0ddjob/Amstrad-CPC/Amstrad_CPC_Keyboard/Connectors/CPC664_Keyboard_Connector.jpeg

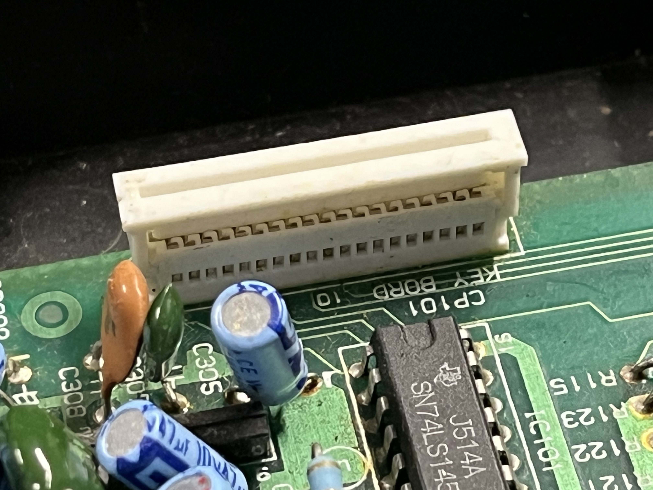
Amstrad_CPC_Keyboard/Connectors/CPC664_Keyboard_Connector.jpeg
