0ddjob/Amstrad-CPC/Amstrad_CPC_Keyboard/Connectors/Later_CPC464_Dual_Keyboard_Connectors.jpeg

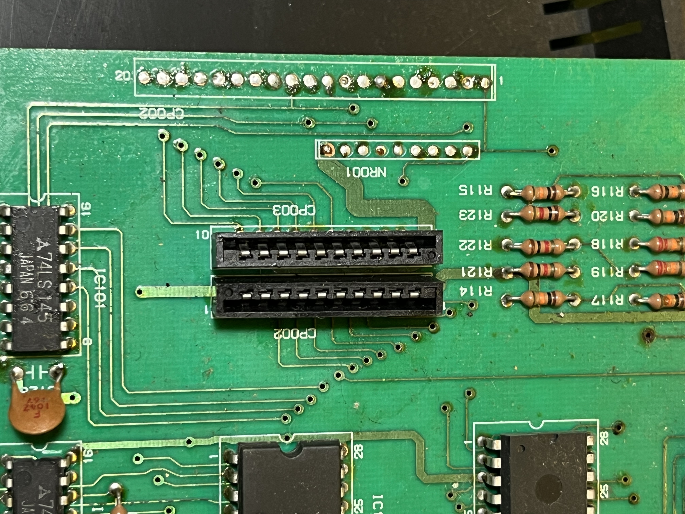
Amstrad_CPC_Keyboard/Connectors/Later_CPC464_Dual_Keyboard_Connectors.jpeg
