0ddjob/Amstrad-CPC/Amstrad_CPC_Keyboard/Connectors/Original_CPC464_20pin_Keyboard_Connector.jpeg

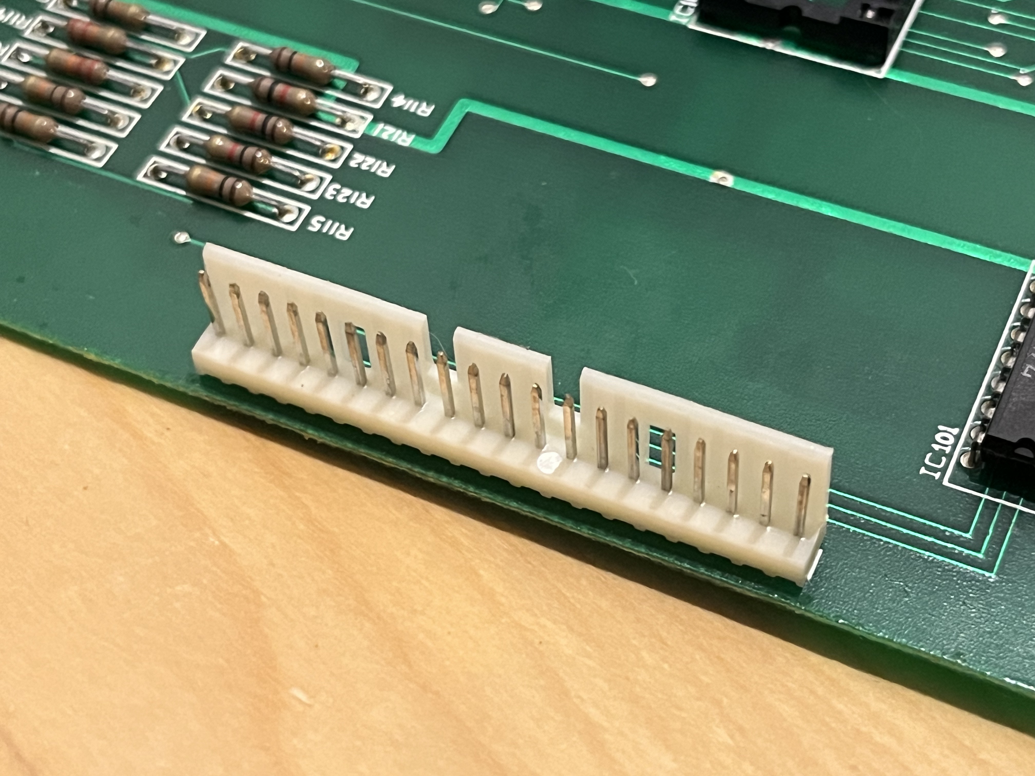
Amstrad_CPC_Keyboard/Connectors/Original_CPC464_20pin_Keyboard_Connector.jpeg
