0ddjob/Amstrad-CPC/Amstrad_CPC_Keyboard/CPC464_CPC664/Keyboard-Layout-Editor/Match_Original_CPC664/amstrad-cpc664_original.jpg

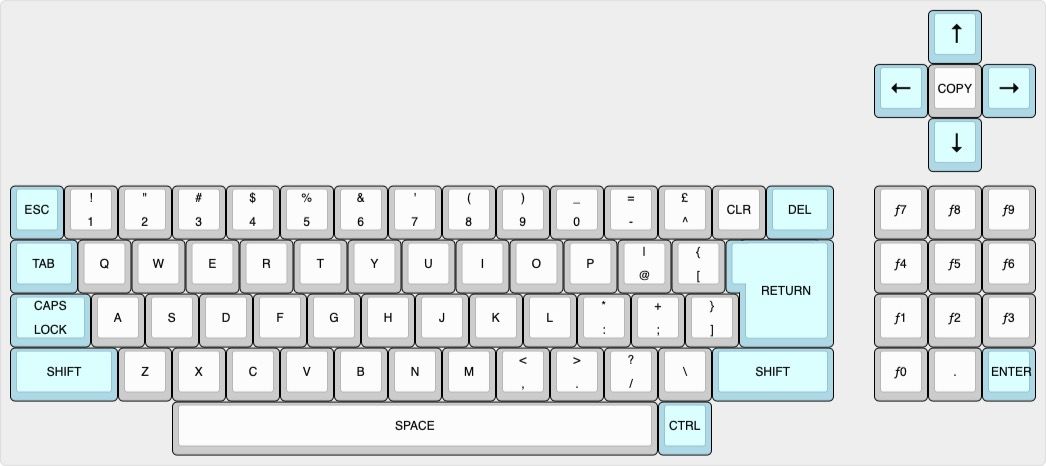
Amstrad_CPC_Keyboard/CPC464_CPC664/Keyboard-Layout-Editor/Match_Original_CPC664/amstrad-cpc664_original.jpg
