0ddjob/Amstrad-CPC/Amstrad_CPC_Keyboard/CPC464_CPC664/Keyboard-Layout-Editor/Modern_Key_Size/amstrad-cpc664_modern.jpg

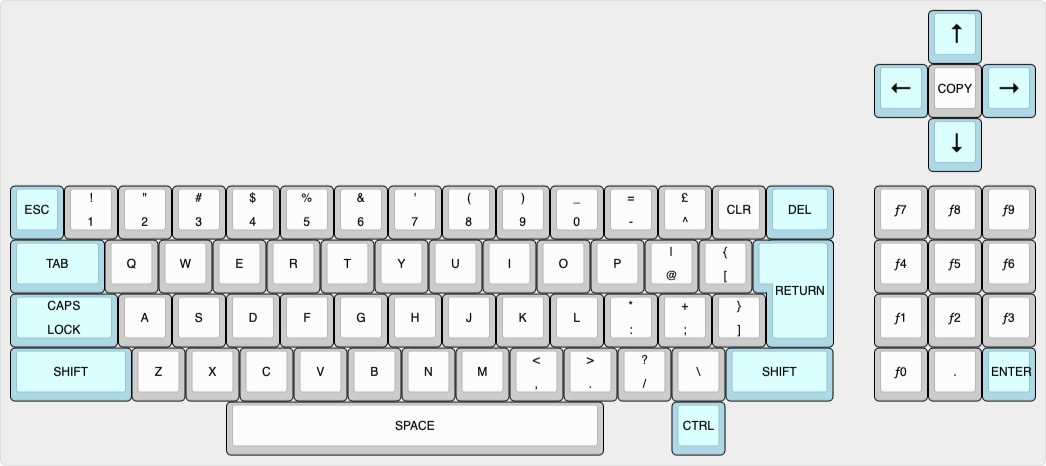
Amstrad_CPC_Keyboard/CPC464_CPC664/Keyboard-Layout-Editor/Modern_Key_Size/amstrad-cpc664_modern.jpg
