0ddjob/Amstrad-CPC/Amstrad_CPC_Keyboard/Datasheets/Amstrad_CPC464_CP002&CP003.jpg

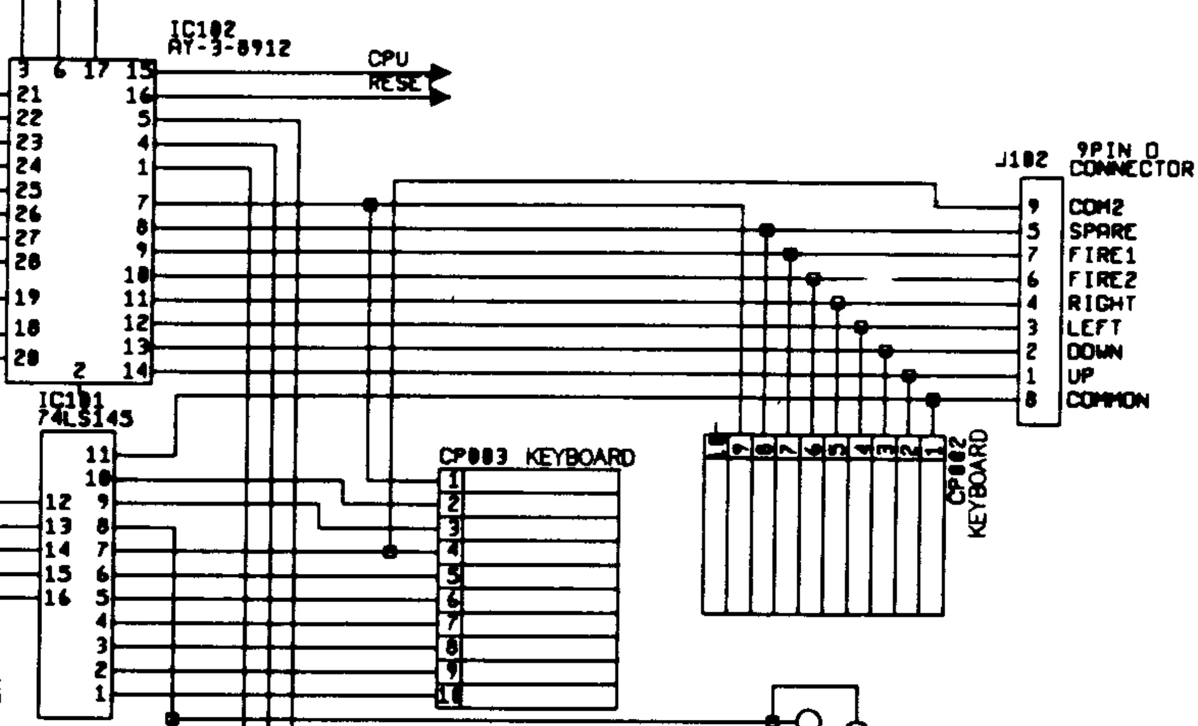
Amstrad_CPC_Keyboard/Datasheets/Amstrad_CPC464_CP002&CP003.jpg
