0ddjob/Amstrad-CPC/Amstrad_CPC_Keyboard/Datasheets/Amstrad_CPC464_MC0044A_Keyboard.jpg

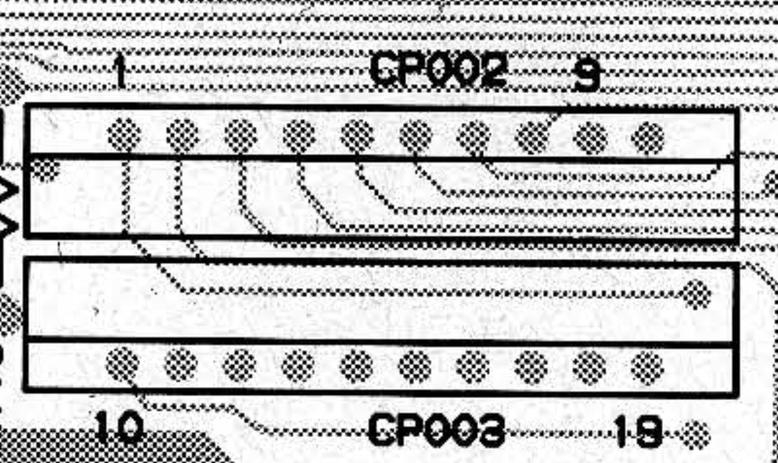
Amstrad_CPC_Keyboard/Datasheets/Amstrad_CPC464_MC0044A_Keyboard.jpg
