0ddjob/Amstrad-CPC/Amstrad_CPC_Keyboard/Schematics/Amstrad_CPC6128_Keyboard_Schematic.png

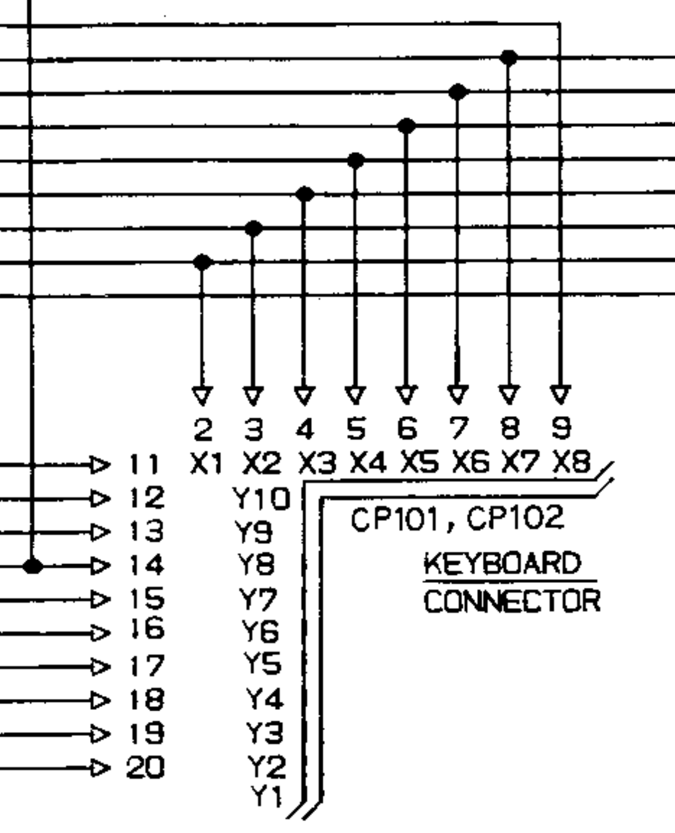
Amstrad_CPC_Keyboard/Schematics/Amstrad_CPC6128_Keyboard_Schematic.png
