0ddjob/Amstrad-CPC/CPC_Plus_Floppy_Adaptor/Amstrad_CPC_Plus_External_drive_connector_pinout.jpg

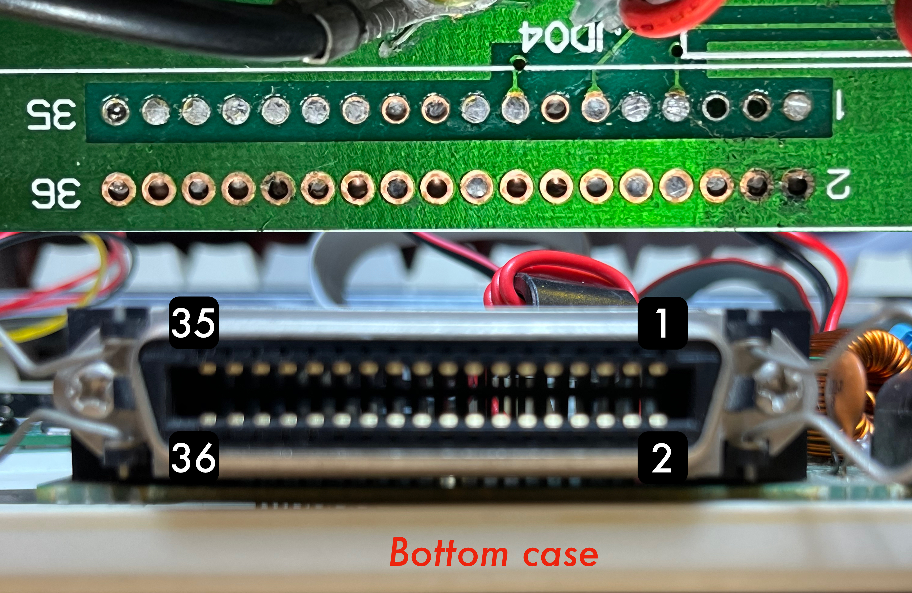
CPC_Plus_Floppy_Adaptor/Amstrad_CPC_Plus_External_drive_connector_pinout.jpg
