0ddjob/Amstrad-CPC/Laserwarp/Sprites/Laserwarp_Sprites.png

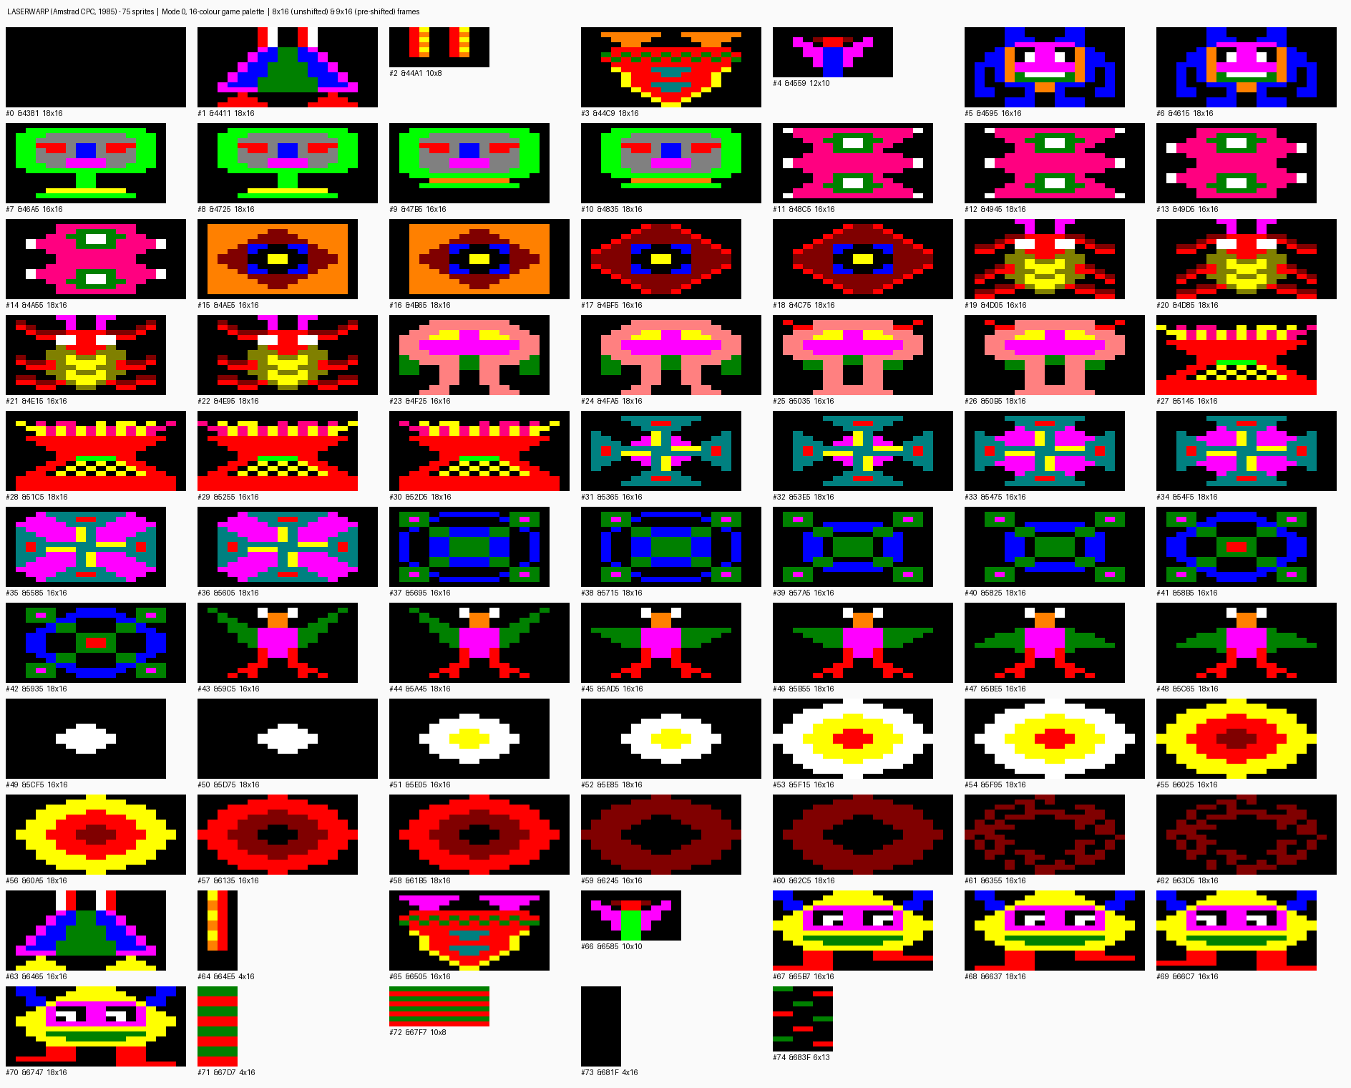
Laserwarp/Sprites/Laserwarp_Sprites.png
