0ddjob/Amstrad-CPC/Laserwarp/Sprites/sprite_01_4411_18x16.png

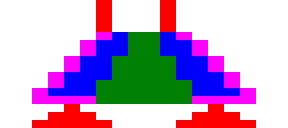
Laserwarp/Sprites/sprite_01_4411_18x16.png
