0ddjob/Amstrad-CPC/Laserwarp/Sprites/sprite_03_44C9_18x16.png

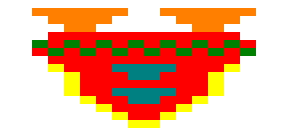
Laserwarp/Sprites/sprite_03_44C9_18x16.png
