0ddjob/Amstrad-CPC/Laserwarp/Sprites/sprite_05_4595_16x16.png

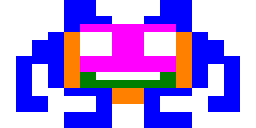
Laserwarp/Sprites/sprite_05_4595_16x16.png
