0ddjob/Amstrad-CPC/Laserwarp/Sprites/sprite_06_4615_18x16.png

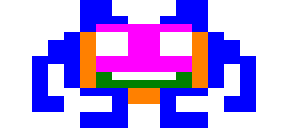
Laserwarp/Sprites/sprite_06_4615_18x16.png
