0ddjob/Amstrad-CPC/Laserwarp/Sprites/sprite_07_46A5_16x16.png

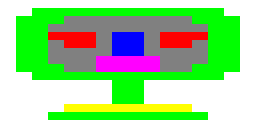
Laserwarp/Sprites/sprite_07_46A5_16x16.png
