0ddjob/Amstrad-CPC/Laserwarp/Sprites/sprite_09_47B5_16x16.png

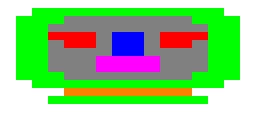
Laserwarp/Sprites/sprite_09_47B5_16x16.png
