0ddjob/Amstrad-CPC/Laserwarp/Sprites/sprite_11_48C5_16x16.png

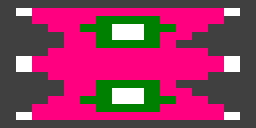
Laserwarp/Sprites/sprite_11_48C5_16x16.png
