0ddjob/Amstrad-CPC/Laserwarp/Sprites/sprite_12_4945_18x16.png

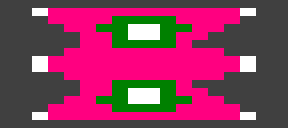
Laserwarp/Sprites/sprite_12_4945_18x16.png
