0ddjob/Amstrad-CPC/Laserwarp/Sprites/sprite_13_49D5_16x16.png

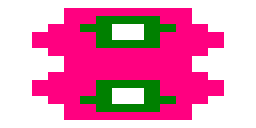
Laserwarp/Sprites/sprite_13_49D5_16x16.png
