0ddjob/Amstrad-CPC/Laserwarp/Sprites/sprite_14_4A55_18x16.png

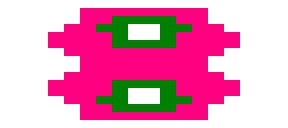
Laserwarp/Sprites/sprite_14_4A55_18x16.png
