0ddjob/Amstrad-CPC/Laserwarp/Sprites/sprite_15_4AE5_16x16.png

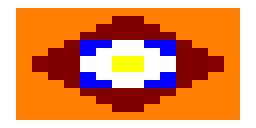
Laserwarp/Sprites/sprite_15_4AE5_16x16.png
