0ddjob/Amstrad-CPC/Laserwarp/Sprites/sprite_17_4BF5_16x16.png

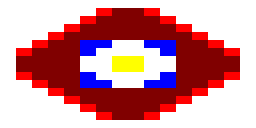
Laserwarp/Sprites/sprite_17_4BF5_16x16.png
