0ddjob/Amstrad-CPC/Laserwarp/Sprites/sprite_18_4C75_18x16.png

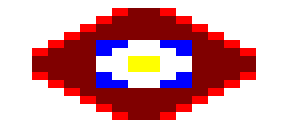
Laserwarp/Sprites/sprite_18_4C75_18x16.png
