0ddjob/Amstrad-CPC/Laserwarp/Sprites/sprite_19_4D05_16x16.png

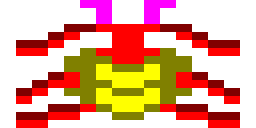
Laserwarp/Sprites/sprite_19_4D05_16x16.png
