0ddjob/Amstrad-CPC/Laserwarp/Sprites/sprite_20_4D85_18x16.png

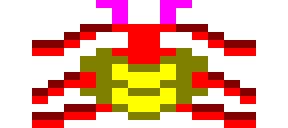
Laserwarp/Sprites/sprite_20_4D85_18x16.png
