0ddjob/Amstrad-CPC/Laserwarp/Sprites/sprite_21_4E15_16x16.png

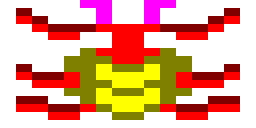
Laserwarp/Sprites/sprite_21_4E15_16x16.png
