0ddjob/Amstrad-CPC/Laserwarp/Sprites/sprite_22_4E95_18x16.png

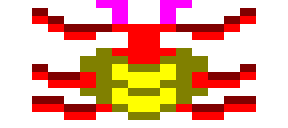
Laserwarp/Sprites/sprite_22_4E95_18x16.png
