0ddjob/Amstrad-CPC/Laserwarp/Sprites/sprite_23_4F25_16x16.png

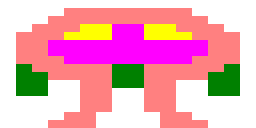
Laserwarp/Sprites/sprite_23_4F25_16x16.png
