0ddjob/Amstrad-CPC/Laserwarp/Sprites/sprite_24_4FA5_18x16.png

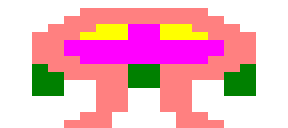
Laserwarp/Sprites/sprite_24_4FA5_18x16.png
