0ddjob/Amstrad-CPC/Laserwarp/Sprites/sprite_25_5035_16x16.png

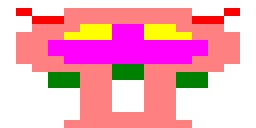
Laserwarp/Sprites/sprite_25_5035_16x16.png
