0ddjob/Amstrad-CPC/Laserwarp/Sprites/sprite_26_50B5_18x16.png

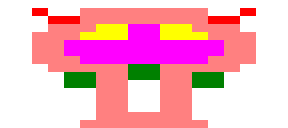
Laserwarp/Sprites/sprite_26_50B5_18x16.png
