0ddjob/Amstrad-CPC/Laserwarp/Sprites/sprite_27_5145_16x16.png

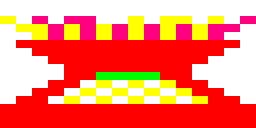
Laserwarp/Sprites/sprite_27_5145_16x16.png
