0ddjob/Amstrad-CPC/Laserwarp/Sprites/sprite_28_51C5_18x16.png

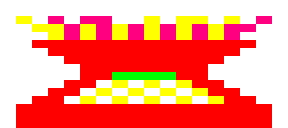
Laserwarp/Sprites/sprite_28_51C5_18x16.png
