0ddjob/Amstrad-CPC/Laserwarp/Sprites/sprite_29_5255_16x16.png

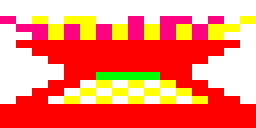
Laserwarp/Sprites/sprite_29_5255_16x16.png
