0ddjob/Amstrad-CPC/Laserwarp/Sprites/sprite_31_5365_16x16.png

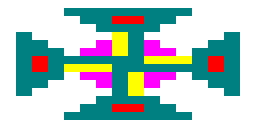
Laserwarp/Sprites/sprite_31_5365_16x16.png
