0ddjob/Amstrad-CPC/Laserwarp/Sprites/sprite_32_53E5_18x16.png

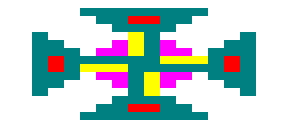
Laserwarp/Sprites/sprite_32_53E5_18x16.png
