0ddjob/Amstrad-CPC/Laserwarp/Sprites/sprite_33_5475_16x16.png

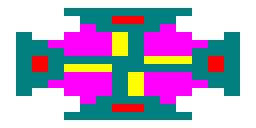
Laserwarp/Sprites/sprite_33_5475_16x16.png
