0ddjob/Amstrad-CPC/Laserwarp/Sprites/sprite_34_54F5_18x16.png

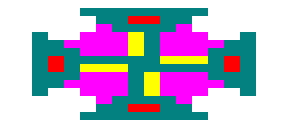
Laserwarp/Sprites/sprite_34_54F5_18x16.png
