0ddjob/Amstrad-CPC/Laserwarp/Sprites/sprite_35_5585_16x16.png

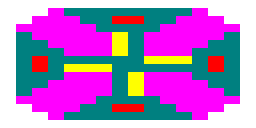
Laserwarp/Sprites/sprite_35_5585_16x16.png
