0ddjob/Amstrad-CPC/Laserwarp/Sprites/sprite_36_5605_18x16.png

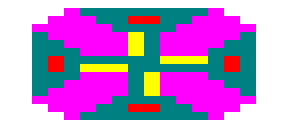
Laserwarp/Sprites/sprite_36_5605_18x16.png
