0ddjob/Amstrad-CPC/Laserwarp/Sprites/sprite_37_5695_16x16.png

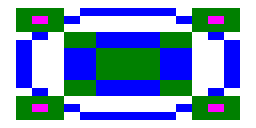
Laserwarp/Sprites/sprite_37_5695_16x16.png
