0ddjob/Amstrad-CPC/Laserwarp/Sprites/sprite_38_5715_18x16.png

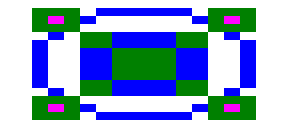
Laserwarp/Sprites/sprite_38_5715_18x16.png
