0ddjob/Amstrad-CPC/Laserwarp/Sprites/sprite_39_57A5_16x16.png

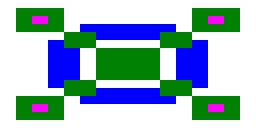
Laserwarp/Sprites/sprite_39_57A5_16x16.png
