0ddjob/Amstrad-CPC/Laserwarp/Sprites/sprite_40_5825_18x16.png

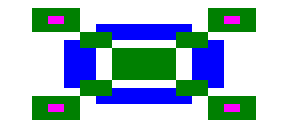
Laserwarp/Sprites/sprite_40_5825_18x16.png
