0ddjob/Amstrad-CPC/Laserwarp/Sprites/sprite_41_58B5_16x16.png

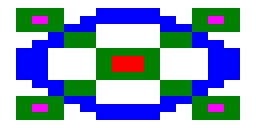
Laserwarp/Sprites/sprite_41_58B5_16x16.png
