0ddjob/Amstrad-CPC/Laserwarp/Sprites/sprite_43_59C5_16x16.png

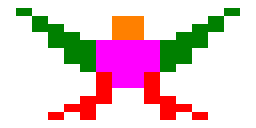
Laserwarp/Sprites/sprite_43_59C5_16x16.png
