0ddjob/Amstrad-CPC/Laserwarp/Sprites/sprite_44_5A45_18x16.png

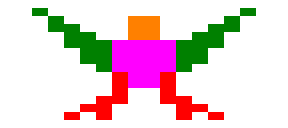
Laserwarp/Sprites/sprite_44_5A45_18x16.png
