0ddjob/Amstrad-CPC/Laserwarp/Sprites/sprite_45_5AD5_16x16.png

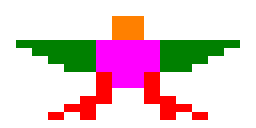
Laserwarp/Sprites/sprite_45_5AD5_16x16.png
