0ddjob/Amstrad-CPC/Laserwarp/Sprites/sprite_47_5BE5_16x16.png

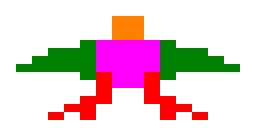
Laserwarp/Sprites/sprite_47_5BE5_16x16.png
