0ddjob/Amstrad-CPC/Laserwarp/Sprites/sprite_48_5C65_18x16.png

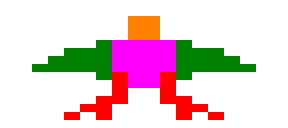
Laserwarp/Sprites/sprite_48_5C65_18x16.png
