0ddjob/Amstrad-CPC/Laserwarp/Sprites/sprite_49_5CF5_16x16.png

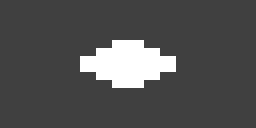
Laserwarp/Sprites/sprite_49_5CF5_16x16.png
