0ddjob/Amstrad-CPC/Laserwarp/Sprites/sprite_50_5D75_18x16.png

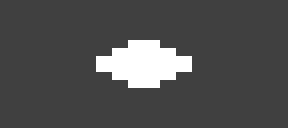
Laserwarp/Sprites/sprite_50_5D75_18x16.png
