0ddjob/Amstrad-CPC/Laserwarp/Sprites/sprite_51_5E05_16x16.png

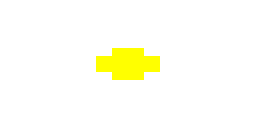
Laserwarp/Sprites/sprite_51_5E05_16x16.png
