0ddjob/Amstrad-CPC/Laserwarp/Sprites/sprite_53_5F15_16x16.png

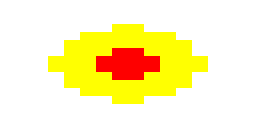
Laserwarp/Sprites/sprite_53_5F15_16x16.png
