0ddjob/Amstrad-CPC/Laserwarp/Sprites/sprite_54_5F95_18x16.png

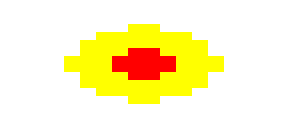
Laserwarp/Sprites/sprite_54_5F95_18x16.png
