0ddjob/Amstrad-CPC/Laserwarp/Sprites/sprite_55_6025_16x16.png

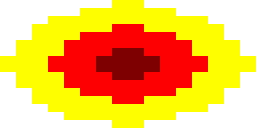
Laserwarp/Sprites/sprite_55_6025_16x16.png
