0ddjob/Amstrad-CPC/Laserwarp/Sprites/sprite_56_60A5_18x16.png

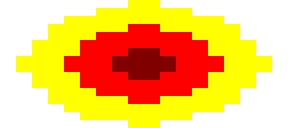
Laserwarp/Sprites/sprite_56_60A5_18x16.png
