0ddjob/Amstrad-CPC/Laserwarp/Sprites/sprite_57_6135_16x16.png

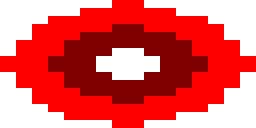
Laserwarp/Sprites/sprite_57_6135_16x16.png
