0ddjob/Amstrad-CPC/Laserwarp/Sprites/sprite_58_61B5_18x16.png

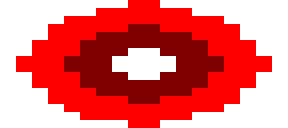
Laserwarp/Sprites/sprite_58_61B5_18x16.png
