0ddjob/Amstrad-CPC/Laserwarp/Sprites/sprite_59_6245_16x16.png

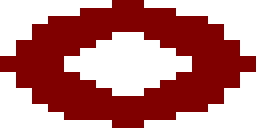
Laserwarp/Sprites/sprite_59_6245_16x16.png
