0ddjob/Amstrad-CPC/Laserwarp/Sprites/sprite_61_6355_16x16.png

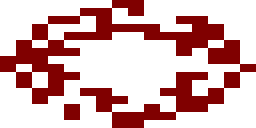
Laserwarp/Sprites/sprite_61_6355_16x16.png
