0ddjob/Amstrad-CPC/Laserwarp/Sprites/sprite_62_63D5_18x16.png

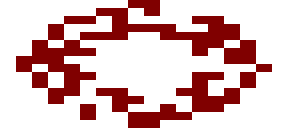
Laserwarp/Sprites/sprite_62_63D5_18x16.png
