0ddjob/Amstrad-CPC/Laserwarp/Sprites/sprite_63_6465_16x16.png

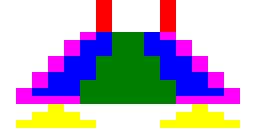
Laserwarp/Sprites/sprite_63_6465_16x16.png
