0ddjob/Amstrad-CPC/Laserwarp/Sprites/sprite_70_6747_18x16.png

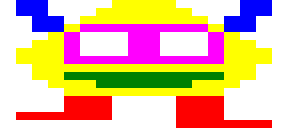
Laserwarp/Sprites/sprite_70_6747_18x16.png
