0ddjob/Amstrad-CPC/VGA4CPC_Brett/Comparator_Board/Comparator_Board_3D.png

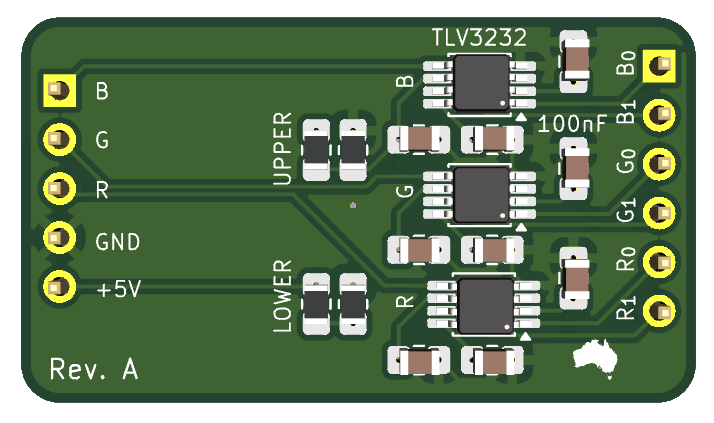
VGA4CPC_Brett/Comparator_Board/Comparator_Board_3D.png
