0ddjob/Amstrad-CPC/Amstrad_CPC_Keyboard/Amstrad_CPC_Tactile-6mm_Troubleshooting_Keyboard.png

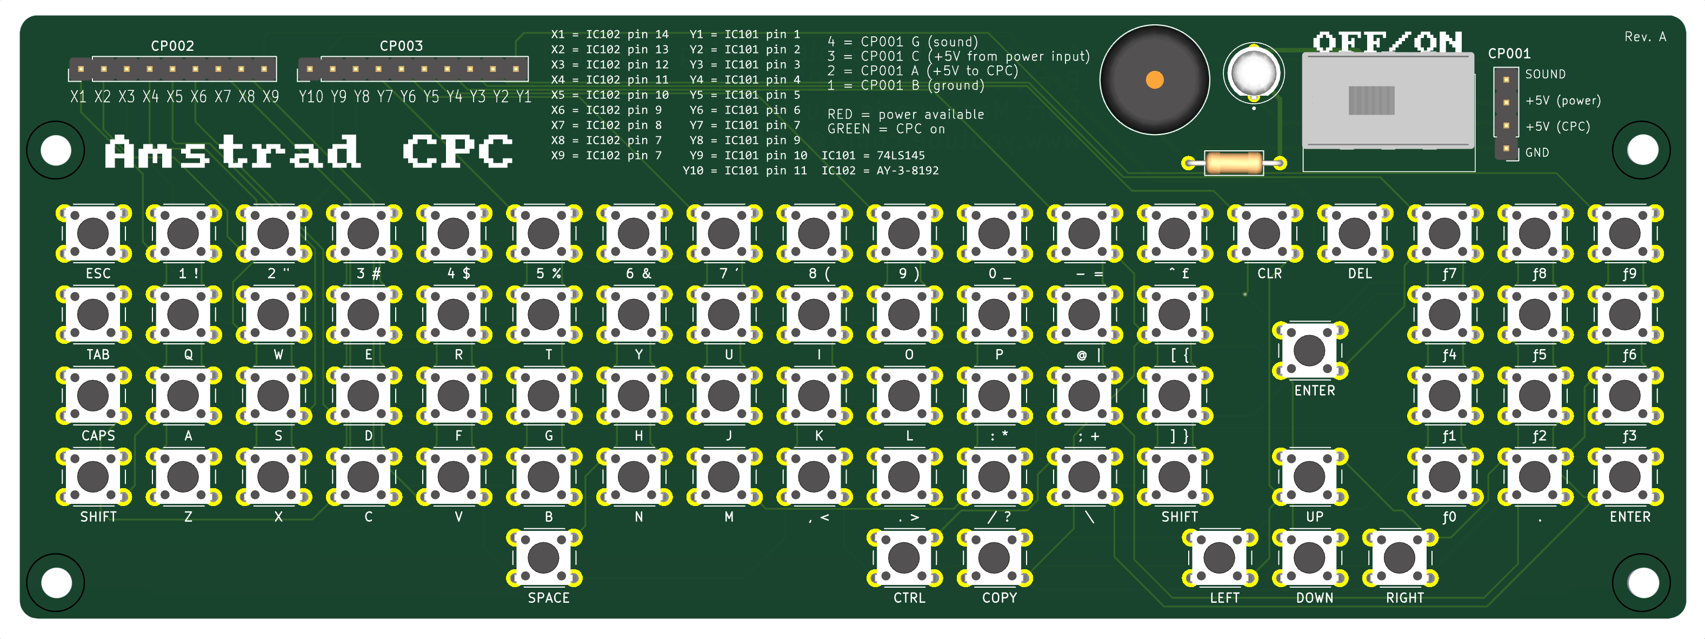
Amstrad_CPC_Keyboard/Amstrad_CPC_Tactile-6mm_Troubleshooting_Keyboard.png
