0ddjob/Amstrad-CPC/Amstrad_CPC_Keyboard/Amstrad_CPC_Tactile-12mm_Troubleshooting_Keyboard_Built.png

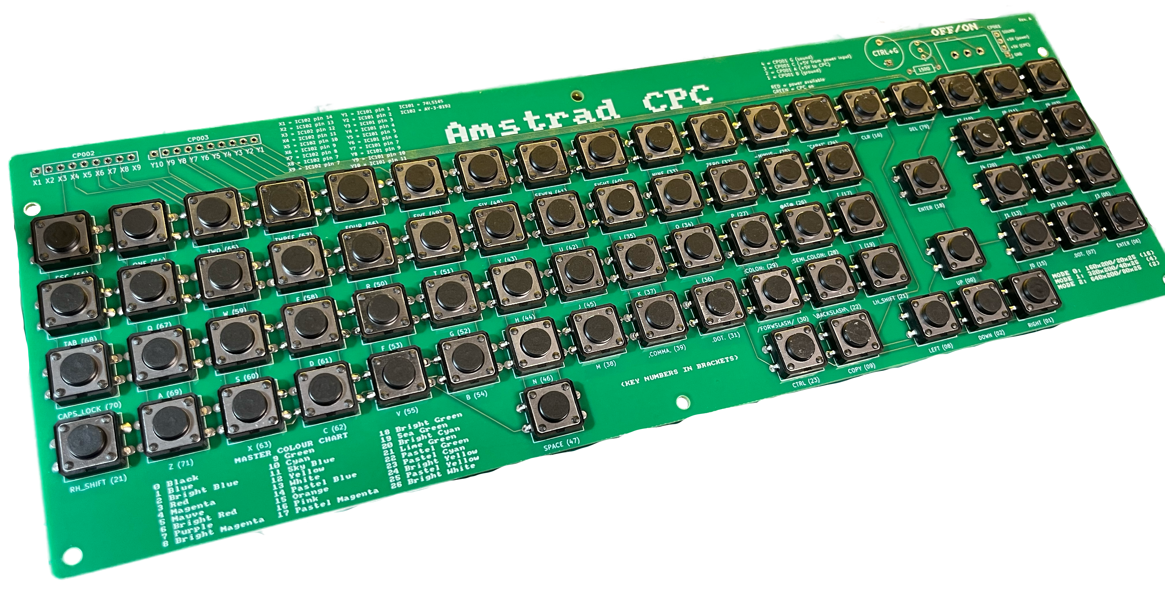
Amstrad_CPC_Keyboard/Amstrad_CPC_Tactile-12mm_Troubleshooting_Keyboard_Built.png
