0ddjob/Amstrad-CPC/Amstrad_CPC_Keyboard/Amstrad_CPC_Tactile_Troubleshooting_Keyboard.png

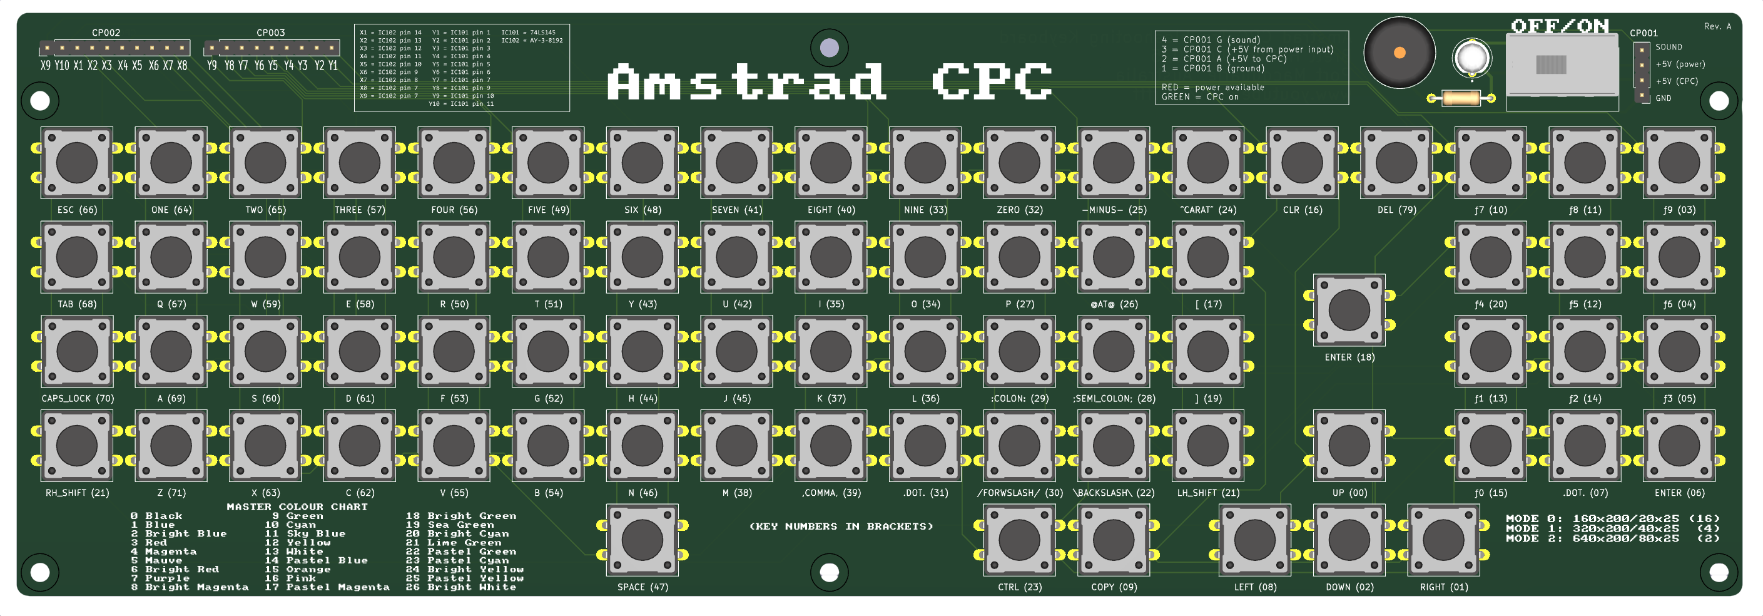
Amstrad_CPC_Keyboard/Amstrad_CPC_Tactile_Troubleshooting_Keyboard.png
