0ddjob/Amstrad-CPC/VGA4CPC_Brett/RevD/VGA4CPC_Brett_RevD_Schematic.pdf

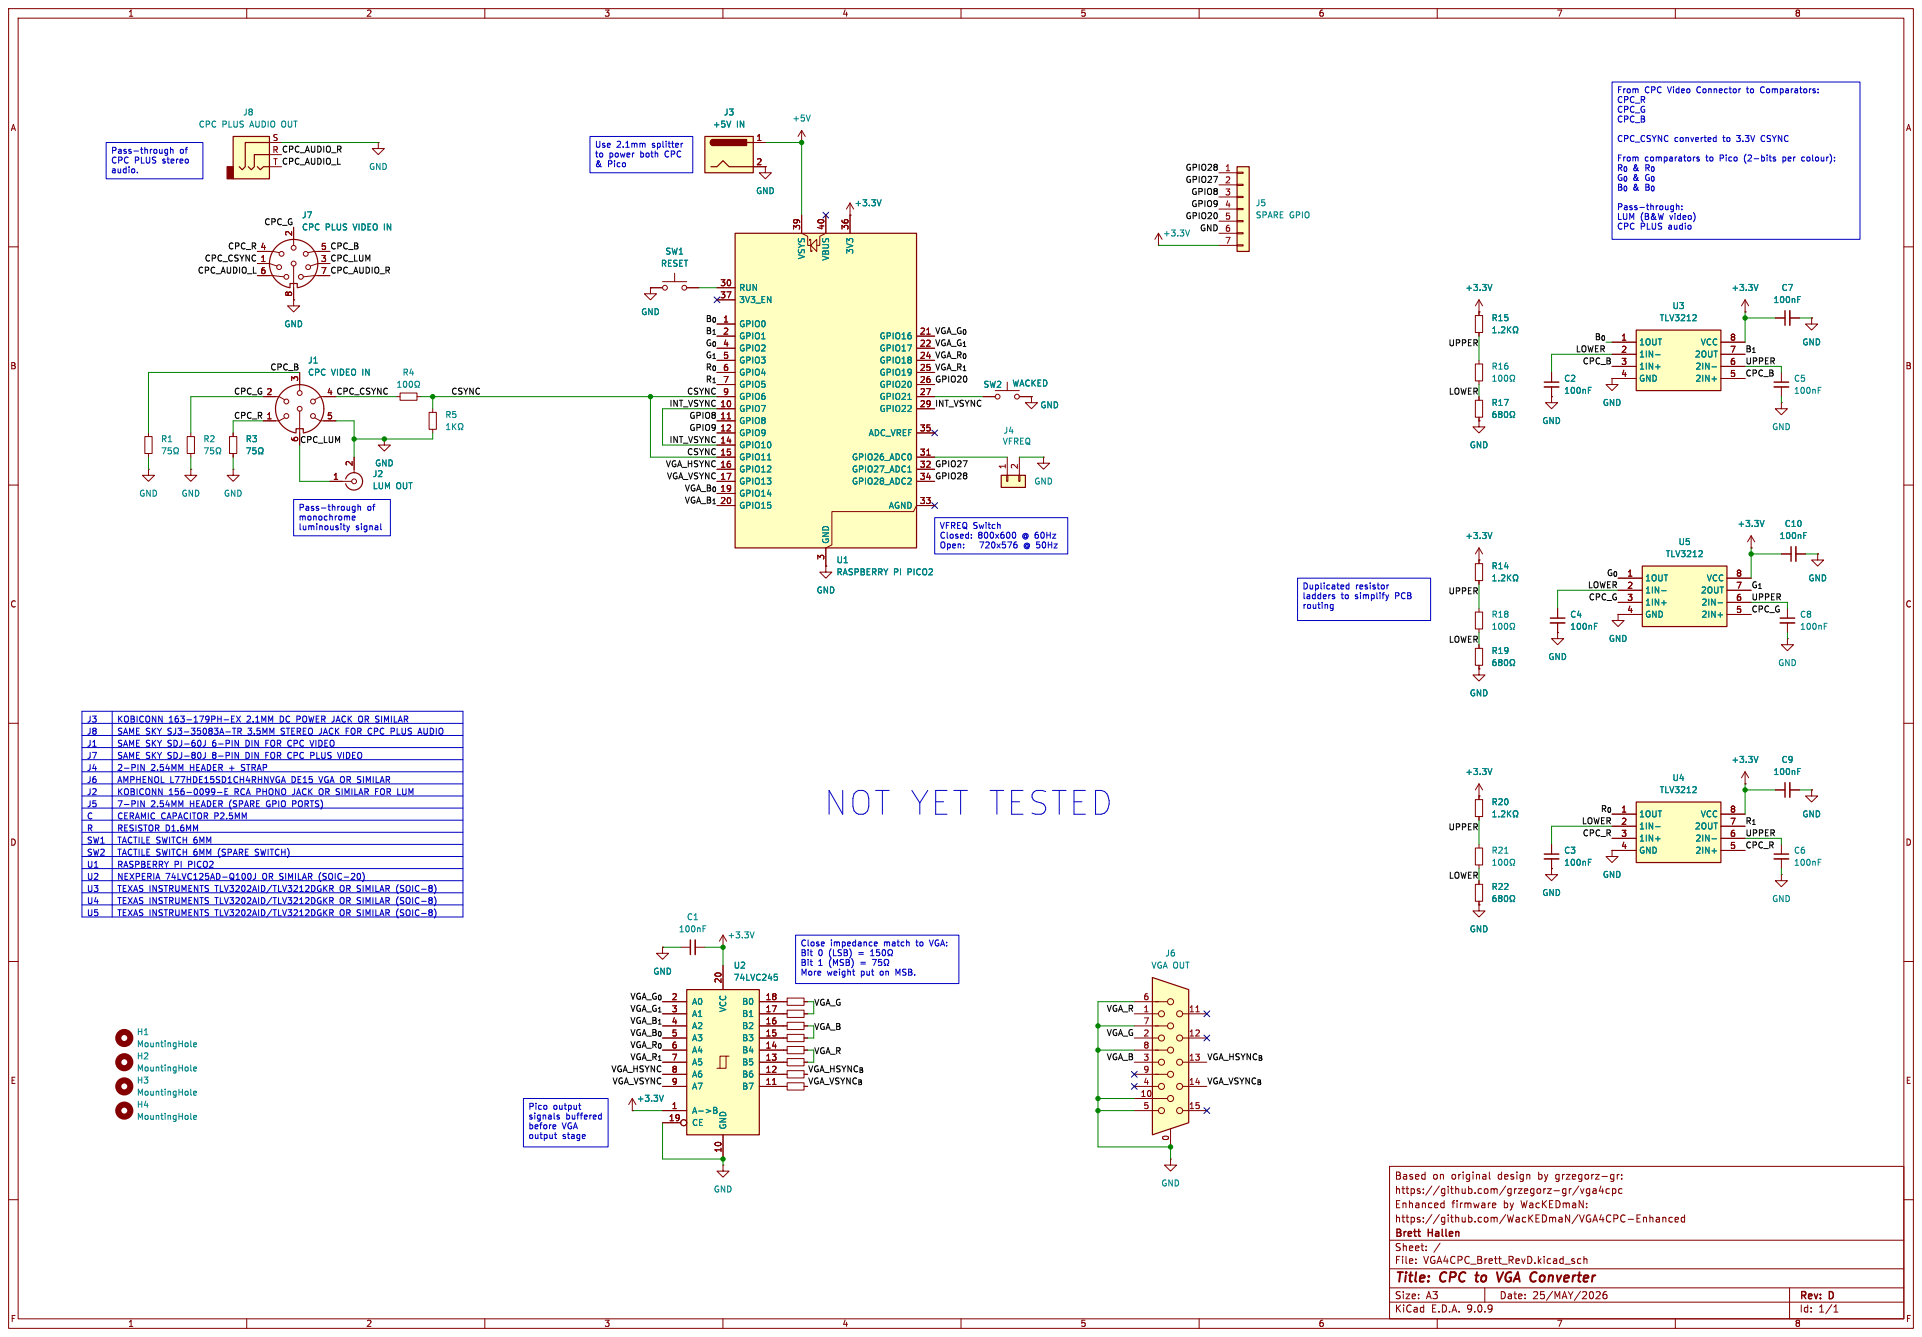
[picture p103: page 1]

to power both CPC

Pass-through: LUM (B&W video) CPC PLUS audio NOT YET TESTED

routing Pico output signals buffered

Bit 1 (MSB) = þÿ75© More weight put on MSB.
