0ddjob/Amstrad-CPC/Amstrad_CPC_Keyboard/CPC6128/Tactile_12mm/Amstrad_Tactile-12mm_Keyboard.kicad_pcb

## KiCad design Amstrad_CPC_Keyboard/CPC6128/Tactile_12mm/Amstrad_Tactile-12mm_Keyboard.kicad_pcb (2025-08-01)

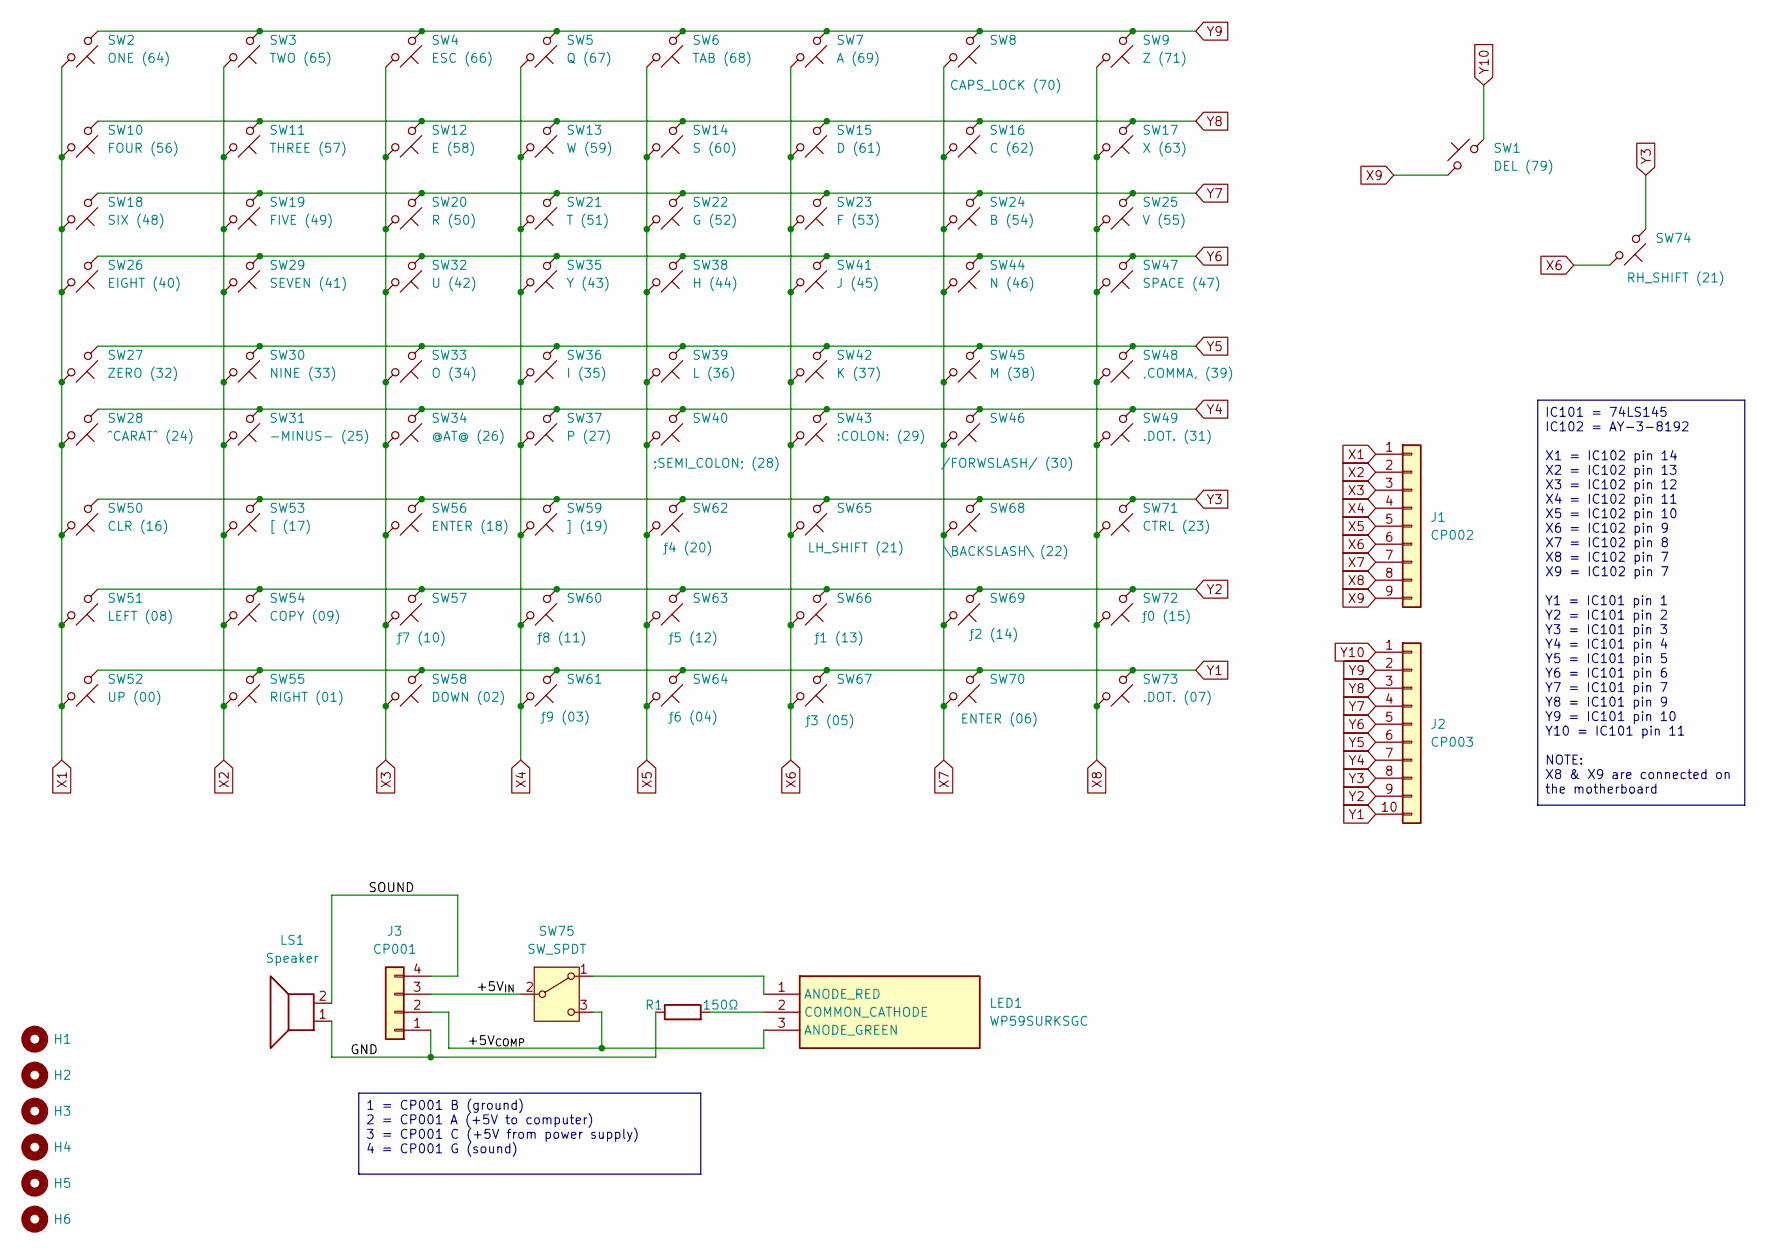
[picture p120: schematic Amstrad_Tactile-12mm_Keyboard.kicad_sch, Amstrad CPC Troubleshooting Keyboard (Tactile)]

Parts:
H1, H2, H3, H4, H5, H6: MountingHole; MountingHole_3.2mm_M3
J1: CP002; PinHeader_1x09_P2.54mm_Vertical
J2: CP003; PinHeader_1x10_P2.54mm_Vertical
J3: CP001; PinHeader_1x04_P2.54mm_Vertical
LED1: WP59SURKSGC; WP59EGC; Mouser Part Number 604-WP59SURKSGC
LS1: Speaker; Buzzer_12x9.5RM7.6
R1: 150Ω; R_Axial_DIN0207_L6.3mm_D2.5mm_P10.16mm_Horizontal
SW1: DEL (79); SW_PUSH-12mm
SW2: ONE (64); SW_PUSH-12mm
SW3: TWO (65); SW_PUSH-12mm
SW4: ESC (66); SW_PUSH-12mm
SW5: Q (67); SW_PUSH-12mm
SW6: TAB (68); SW_PUSH-12mm
SW7: A (69); SW_PUSH-12mm
SW8: CAPS_LOCK (70); SW_PUSH-12mm
SW9: Z (71); SW_PUSH-12mm
SW10: FOUR (56); SW_PUSH-12mm
SW11: THREE (57); SW_PUSH-12mm
SW12: E (58); SW_PUSH-12mm
SW13: W (59); SW_PUSH-12mm
SW14: S (60); SW_PUSH-12mm
SW15: D (61); SW_PUSH-12mm
SW16: C (62); SW_PUSH-12mm
SW17: X (63); SW_PUSH-12mm
SW18: SIX (48); SW_PUSH-12mm
SW19: FIVE (49); SW_PUSH-12mm
SW20: R (50); SW_PUSH-12mm
SW21: T (51); SW_PUSH-12mm
SW22: G (52); SW_PUSH-12mm
SW23: F (53); SW_PUSH-12mm
SW24: B (54); SW_PUSH-12mm
SW25: V (55); SW_PUSH-12mm
SW26: EIGHT (40); SW_PUSH-12mm
SW27: ZERO (32); SW_PUSH-12mm
SW28: ^CARAT^ (24); SW_PUSH-12mm
SW29: SEVEN (41); SW_PUSH-12mm
SW30: NINE (33); SW_PUSH-12mm
SW31: -MINUS- (25); SW_PUSH-12mm
SW32: U (42); SW_PUSH-12mm
SW33: O (34); SW_PUSH-12mm
SW34: @AT@ (26); SW_PUSH-12mm
SW35: Y (43); SW_PUSH-12mm
SW36: I (35); SW_PUSH-12mm
SW37: P (27); SW_PUSH-12mm
SW38: H (44); SW_PUSH-12mm
SW39: L (36); SW_PUSH-12mm
SW40: ;SEMI_COLON; (28); SW_PUSH-12mm
SW41: J (45); SW_PUSH-12mm
SW42: K (37); SW_PUSH-12mm
SW43: :COLON: (29); SW_PUSH-12mm
SW44: N (46); SW_PUSH-12mm
SW45: M (38); SW_PUSH-12mm
SW46: /FORWSLASH/ (30); SW_PUSH-12mm
SW47: SPACE (47); SW_PUSH-12mm
SW48: ,COMMA, (39); SW_PUSH-12mm
SW49: .DOT. (31); SW_PUSH-12mm
SW50: CLR (16); SW_PUSH-12mm
SW51: LEFT (08); SW_PUSH-12mm
SW52: UP (00); SW_PUSH-12mm
SW53: [ (17); SW_PUSH-12mm
SW54: COPY (09); SW_PUSH-12mm
SW55: RIGHT (01); SW_PUSH-12mm
SW56: ENTER (18); SW_PUSH-12mm
SW57: ƒ7 (10); SW_PUSH-12mm
SW58: DOWN (02); SW_PUSH-12mm
SW59: ] (19); SW_PUSH-12mm
SW60: ƒ8 (11); SW_PUSH-12mm
SW61: ƒ9 (03); SW_PUSH-12mm
SW62: ƒ4 (20); SW_PUSH-12mm
SW63: ƒ5 (12); SW_PUSH-12mm
SW64: ƒ6 (04); SW_PUSH-12mm
SW65: LH_SHIFT (21); SW_PUSH-12mm
SW66: ƒ1 (13); SW_PUSH-12mm
SW67: ƒ3 (05); SW_PUSH-12mm
SW68: \BACKSLASH\ (22); SW_PUSH-12mm
SW69: ƒ2 (14); SW_PUSH-12mm
SW70: ENTER (06); SW_PUSH-12mm
SW71: CTRL (23); SW_PUSH-12mm
SW72: ƒ0 (15); SW_PUSH-12mm
SW73: .DOT. (07); SW_PUSH-12mm
SW74: RH_SHIFT (21); SW_PUSH-12mm
SW75: SW_SPDT; L102011MS02Q

Connections:
/+5V_{COMP}: J3.2, LED1.3 (ANODE_GREEN), SW75.3 (C)
/+5V_{IN}: J3.3, SW75.2 (B)
/GND: J3.1, LS1.1, R1.1
/SOUND: J3.4, LS1.2
unnamed: LED1.1 (ANODE_RED), SW75.1 (A)
unnamed: LED1.2 (COMMON_CATHODE), R1.2
X1: J1.1, SW2.2, SW10.2, SW18.2, SW26.2, SW27.2, SW28.2, SW50.2, SW51.2, SW52.2
X2: J1.2, SW3.2, SW11.2, SW19.2, SW29.2, SW30.2, SW31.2, SW53.2, SW54.2, SW55.2
X3: J1.3, SW4.2, SW12.2, SW20.2, SW32.2, SW33.2, SW34.2, SW56.2, SW57.2, SW58.2
X4: J1.4, SW5.2, SW13.2, SW21.2, SW35.2, SW36.2, SW37.2, SW59.2, SW60.2, SW61.2
X5: J1.5, SW6.2, SW14.2, SW22.2, SW38.2, SW39.2, SW40.2, SW62.2, SW63.2, SW64.2
X6: J1.6, SW7.2, SW15.2, SW23.2, SW41.2, SW42.2, SW43.2, SW65.2, SW66.2, SW67.2, SW74.2
X7: J1.7, SW8.2, SW16.2, SW24.2, SW44.2, SW45.2, SW46.2, SW68.2, SW69.2, SW70.2
X8: J1.8, SW9.2, SW17.2, SW25.2, SW47.2, SW48.2, SW49.2, SW71.2, SW72.2, SW73.2
X9: J1.9, SW1.1
Y1: J2.10, SW52.1, SW55.1, SW58.1, SW61.1, SW64.1, SW67.1, SW70.1, SW73.1
Y2: J2.9, SW51.1, SW54.1, SW57.1, SW60.1, SW63.1, SW66.1, SW69.1, SW72.1
Y3: J2.8, SW50.1, SW53.1, SW56.1, SW59.1, SW62.1, SW65.1, SW68.1, SW71.1, SW74.1
Y4: J2.7, SW28.1, SW31.1, SW34.1, SW37.1, SW40.1, SW43.1, SW46.1, SW49.1
Y5: J2.6, SW27.1, SW30.1, SW33.1, SW36.1, SW39.1, SW42.1, SW45.1, SW48.1
Y6: J2.5, SW26.1, SW29.1, SW32.1, SW35.1, SW38.1, SW41.1, SW44.1, SW47.1
Y7: J2.4, SW18.1, SW19.1, SW20.1, SW21.1, SW22.1, SW23.1, SW24.1, SW25.1
Y8: J2.3, SW10.1, SW11.1, SW12.1, SW13.1, SW14.1, SW15.1, SW16.1, SW17.1
Y9: J2.2, SW2.1, SW3.1, SW4.1, SW5.1, SW6.1, SW7.1, SW8.1, SW9.1
Y10: J2.1, SW1.2

Notes on the sheet:
1 = CP001 B (ground) 2 = CP001 A (+5V to computer) 3 = CP001 C (+5V from power supply) 4 = CP001 G (sound)
IC101 = 74LS145 IC102 = AY-3-8192 X1 = IC102 pin 14 X2 = IC102 pin 13 X3 = IC102 pin 12 X4 = IC102 pin 11 X5 = IC102 pin 10 X6 = IC102 pin 9 X7 = IC102 pin 8 X8 = IC102 pin 7 X9 = IC102 pin 7 Y1 = IC101 pin 1 Y2 = IC101 pin 2 Y3 = IC101 pin 3 Y4 = IC101 pin 4 Y5 = IC101 pin 5 Y6 = IC101 pin 6 Y7 = 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

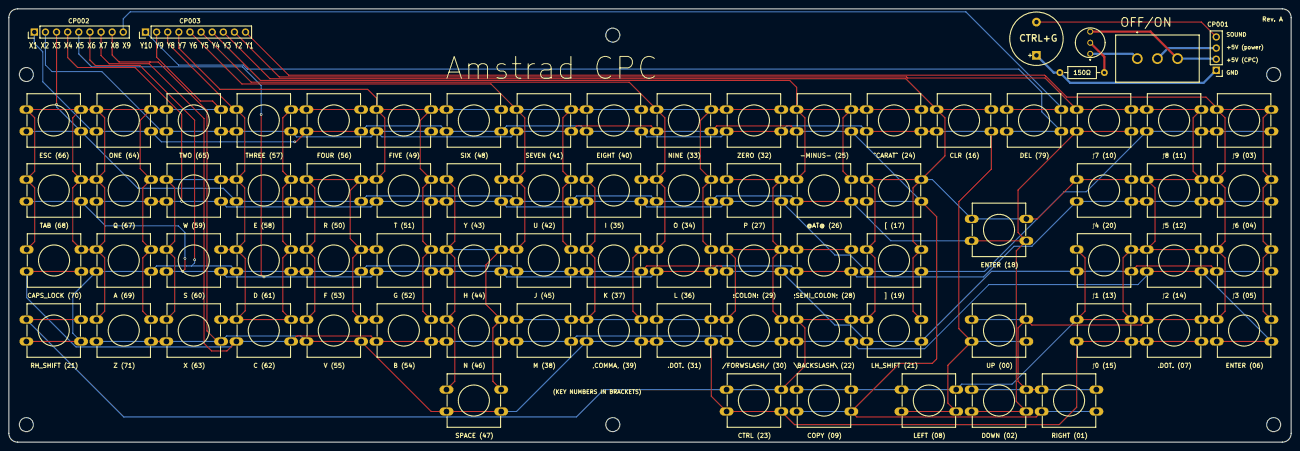
[picture p121: board Amstrad_Tactile-12mm_Keyboard.kicad_pcb from above]

Board: 2 copper layers, 293.0 x 99.0 mm, 87 parts (0 on the bottom side), 25 nets.
