0ddjob/Amstrad-CPC/CPC_PICOROM_PLUS/Hardware/Kicad/CPC_PICOROM_PLUS.kicad_pcb

## KiCad design CPC_PICOROM_PLUS/Hardware/Kicad/CPC_PICOROM_PLUS.kicad_pcb (2025-07-30)

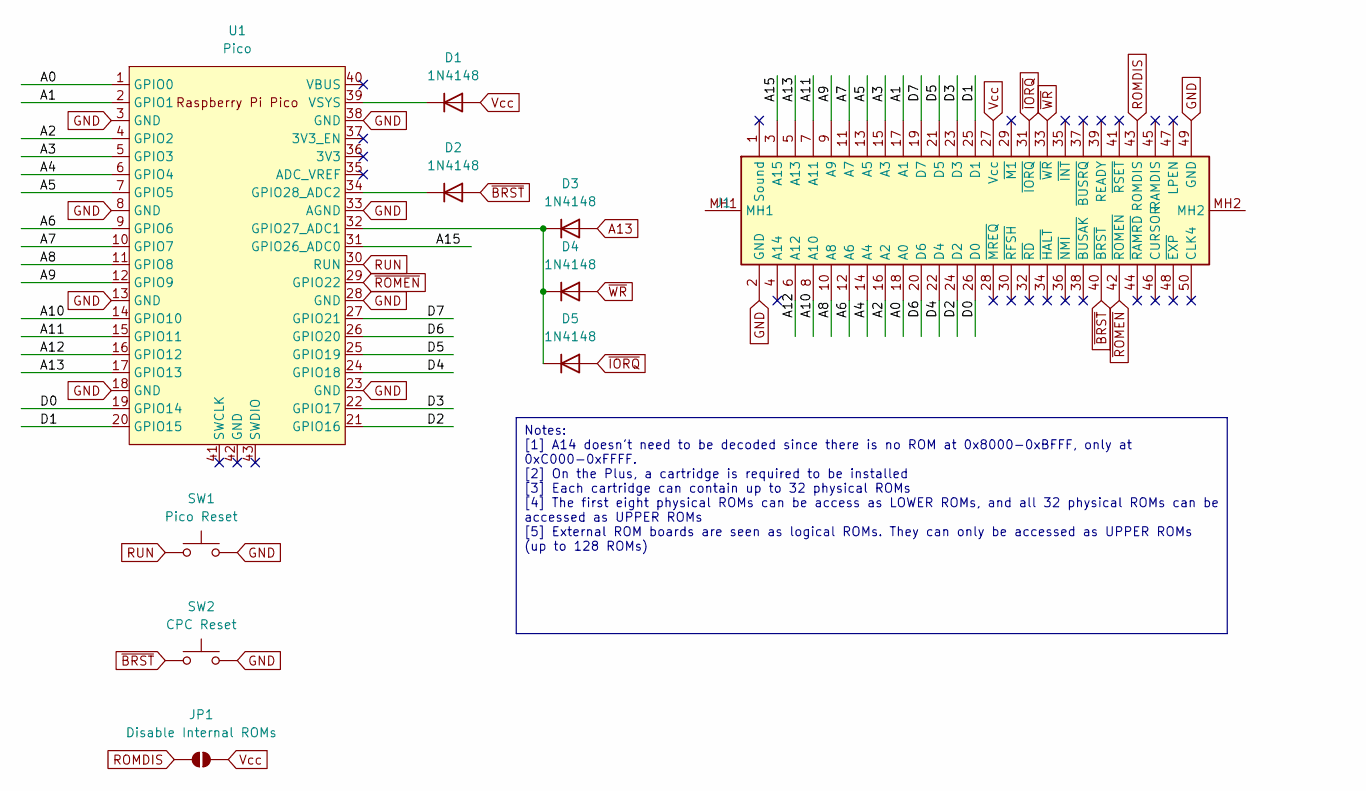
[picture p122: schematic CPC_PICOROM_PLUS.kicad_sch, CPC PicoROM Plus]

Parts:
D1, D2, D3, D4, D5: 1N4148; D_DO-35_SOD27_P7.62mm_Horizontal
J1: Amstrad_CPC_Plus_Expansion; 111050113L001_Amstrad_Plus; Manufacturer_Part_Number 111-050-113L001
JP1: Disable Internal ROMs; SolderJumper-2_P1.3mm_Open_RoundedPad1.0x1.5mm
SW1: Pico Reset; Switch_Tactile_6mm
SW2: CPC Reset; Switch_Tactile_6mm
U1: Pico; RPi_Pico_SMD_TH

Connections:
/A0: J1.18 (A0), U1.1 (GPIO0)
/A1: J1.17 (A1), U1.2 (GPIO1)
/A2: J1.16 (A2), U1.4 (GPIO2)
/A3: J1.15 (A3), U1.5 (GPIO3)
/A4: J1.14 (A4), U1.6 (GPIO4)
/A5: J1.13 (A5), U1.7 (GPIO5)
/A6: J1.12 (A6), U1.9 (GPIO6)
/A7: J1.11 (A7), U1.10 (GPIO7)
/A8: J1.10 (A8), U1.11 (GPIO8)
/A9: J1.9 (A9), U1.12 (GPIO9)
/A10: J1.8 (A10), U1.14 (GPIO10)
/A11: J1.7 (A11), U1.15 (GPIO11)
/A12: J1.6 (A12), U1.16 (GPIO12)
/A15: J1.3 (A15), U1.31 (GPIO26_ADC0)
/D0: J1.26 (D0), U1.19 (GPIO14)
/D1: J1.25 (D1), U1.20 (GPIO15)
/D2: J1.24 (D2), U1.21 (GPIO16)
/D3: J1.23 (D3), U1.22 (GPIO17)
/D4: J1.22 (D4), U1.24 (GPIO18)
/D5: J1.21 (D5), U1.25 (GPIO19)
/D6: J1.20 (D6), U1.26 (GPIO20)
/D7: J1.19 (D7), U1.27 (GPIO21)
A13: D3.2 (A), J1.5 (A13), U1.17 (GPIO13)
GND: J1.2 (GND), J1.49 (GND), SW1.2, SW2.2, U1.3 (GND), U1.8 (GND), U1.13 (GND), U1.18 (GND), U1.23 (GND), U1.28 (GND), U1.33 (AGND), U1.38 (GND)
unnamed: D1.1 (K), U1.39 (VSYS)
unnamed: D2.1 (K), U1.34 (GPIO28_ADC2)
unnamed: D3.1 (K), D4.1 (K), D5.1 (K), U1.32 (GPIO27_ADC1)
ROMDIS: J1.43 (ROMDIS), JP1.1 (A)
RUN: SW1.1, U1.30 (RUN)
Vcc: D1.2 (A), J1.27 (Vcc), JP1.2 (B)
~BRST: D2.2 (A), J1.40 (~BRST), SW2.1
~IORQ: D5.2 (A), J1.31 (~IORQ)
~ROMEN: J1.42 (~ROMEN), U1.29 (GPIO22)
~WR: D4.2 (A), J1.33 (~WR)

Notes on the sheet:
Notes: [1] A14 doesn't need to be decoded since there is no ROM at 0x8000-0xBFFF, only at 0xC000-0xFFFF. [2] On the Plus, a cartridge is required to be installed [3] Each cartridge can contain up to 32 physical ROMs [4] The first eight physical ROMs can be access as LOWER ROMs, and all 32 physical 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

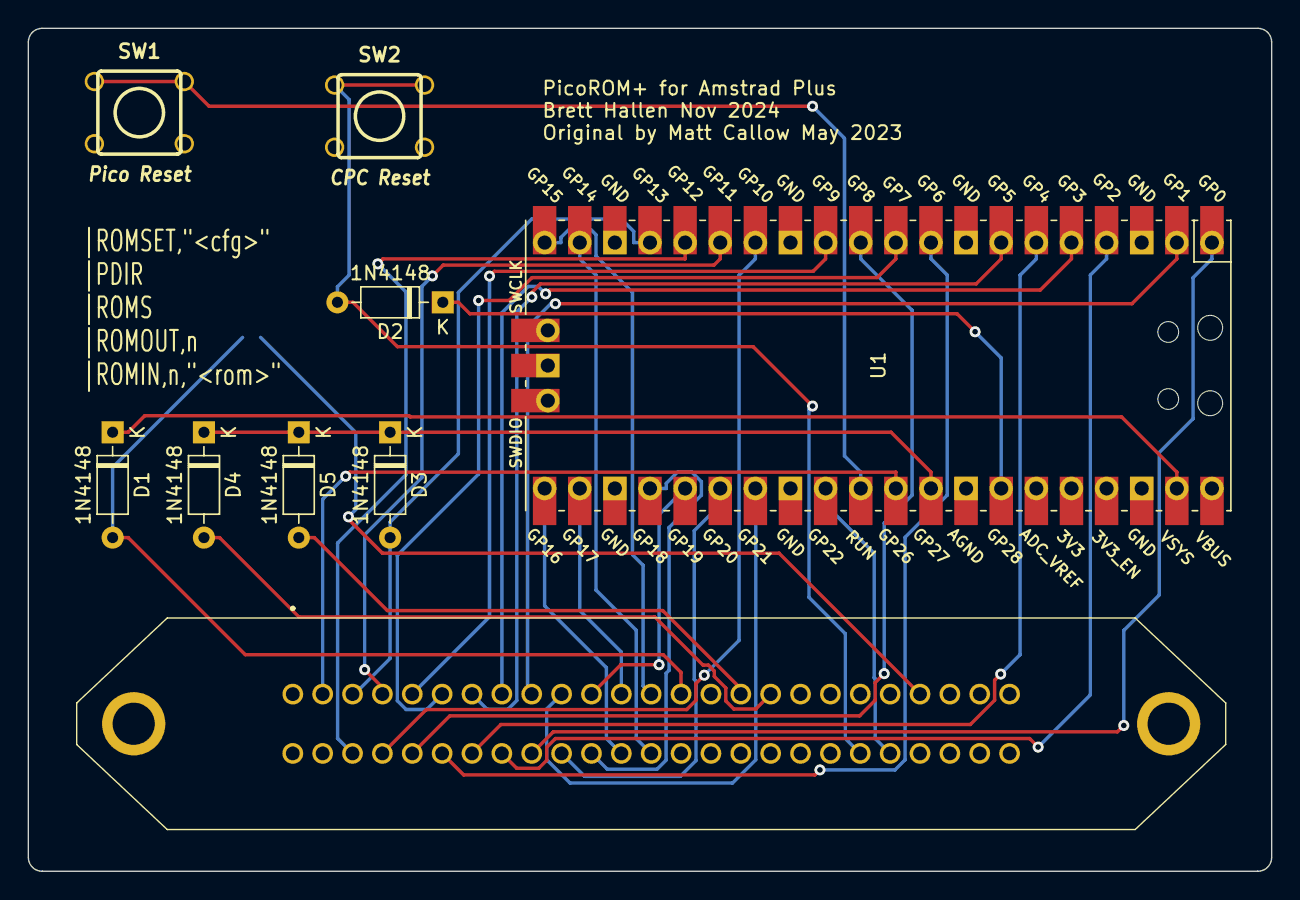
[picture p123: board CPC_PICOROM_PLUS.kicad_pcb from above]

Board: 2 copper layers, 89.9 x 61.0 mm, 10 parts (1 on the bottom side), 34 nets.
