0ddjob/Amstrad-CPC/Easy-Add-on-Projects-for-Amstrad-CPC/Project02/Kicad/Project_02_Picture_Digitiser.kicad_pcb

## KiCad design Easy-Add-on-Projects-for-Amstrad-CPC/Project02/Kicad/Project_02_Picture_Digitiser.kicad_pcb (2025-07-30)

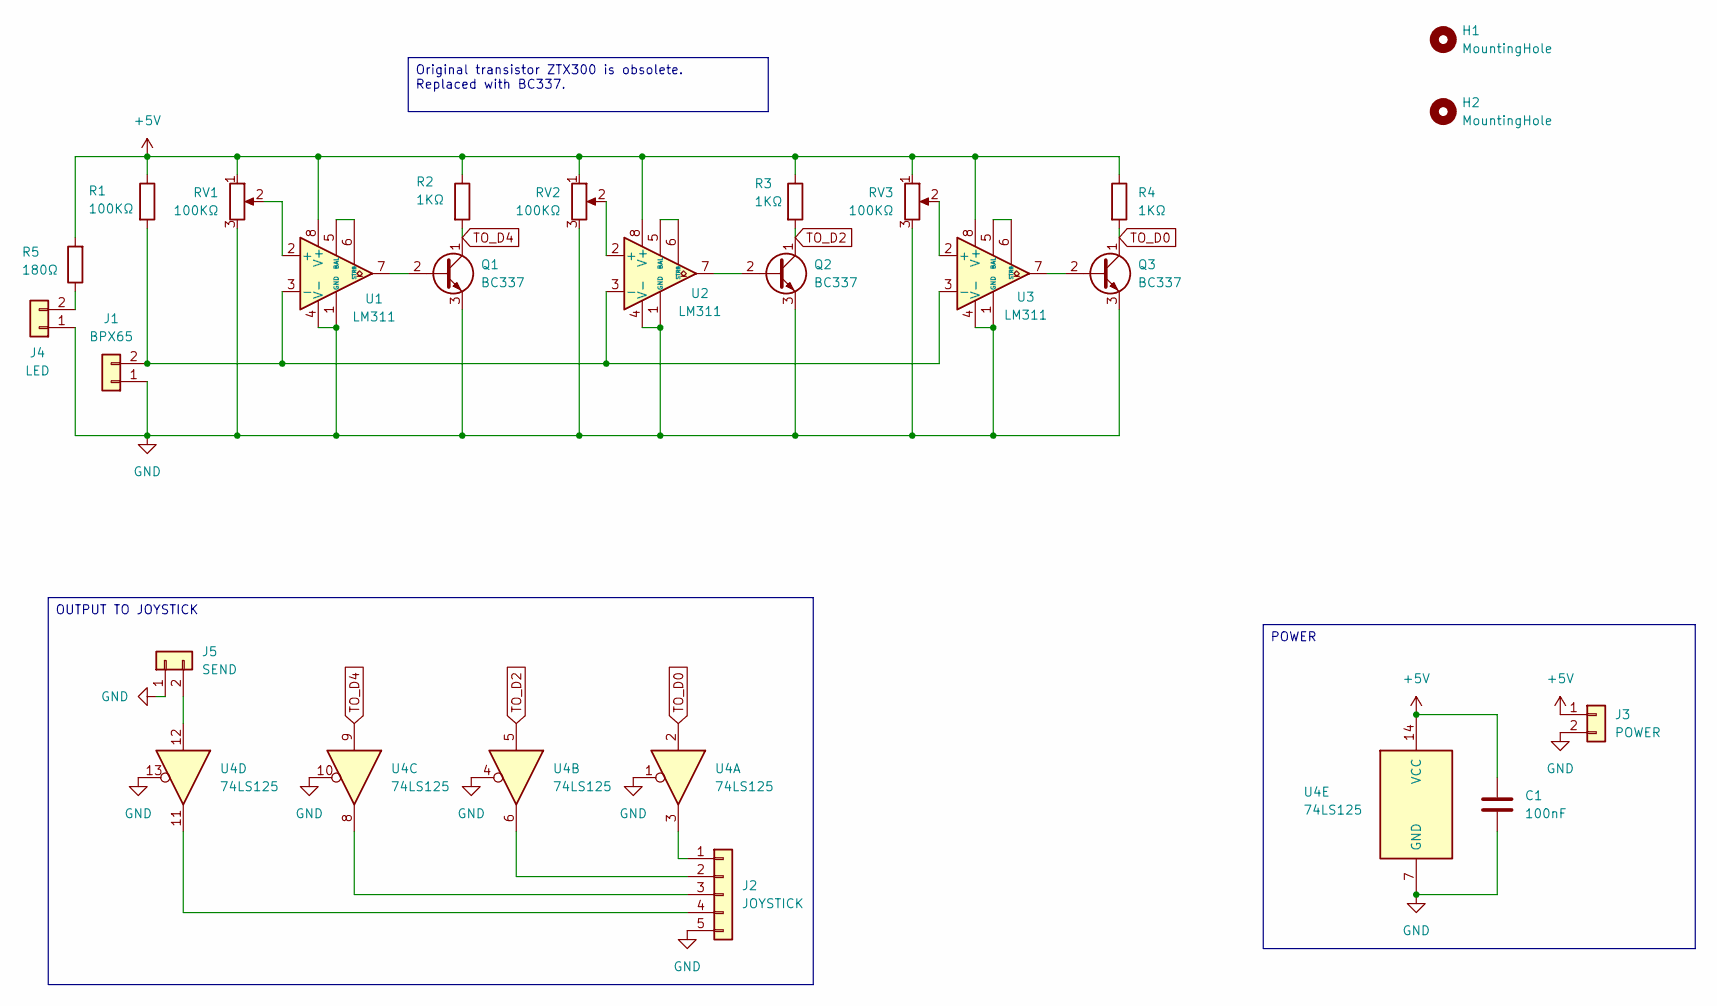
[picture p124: schematic Project_02_Picture_Digitiser.kicad_sch, Project 2: Picture Digitiser]

Parts:
C1: 100nF; C_Disc_D3.4mm_W2.1mm_P2.50mm
H1, H2: MountingHole; MountingHole_3.2mm_M3
J1: BPX65; PinSocket_1x02_P2.54mm_Vertical
J2: JOYSTICK; PinSocket_1x05_P2.54mm_Vertical
J3: POWER; PinSocket_1x02_P2.54mm_Vertical
J4: LED; PinSocket_1x02_P2.54mm_Vertical
J5: SEND; PinSocket_1x02_P2.54mm_Vertical
Q1, Q2, Q3: BC337; TO-92_Inline
R1: 100KΩ; R_Axial_DIN0207_L6.3mm_D2.5mm_P7.62mm_Horizontal
R2, R3, R4: 1KΩ; R_Axial_DIN0207_L6.3mm_D2.5mm_P7.62mm_Horizontal
R5: 180Ω; R_Axial_DIN0207_L6.3mm_D2.5mm_P7.62mm_Horizontal
RV1, RV2, RV3: 100KΩ; Potentiometer_Bourns_3296W_Vertical
U1, U2, U3: LM311; DIP-8_W7.62mm
U4: 74LS125; DIP-14_W7.62mm

Connections:
+5V: C1.1, J3.1, R1.1, R2.1, R3.1, R4.1, R5.2, RV1.1, RV2.1, RV3.1, U1.8 (V+), U2.8 (V+), U3.8 (V+), U4.14 (VCC)
GND: C1.2, J1.1, J2.5, J3.2, J4.1, J5.1, Q1.3 (E), Q2.3 (E), Q3.3 (E), RV1.3, RV2.3, RV3.3, U1.1 (GND), U1.4 (V-), U2.1 (GND), U2.4 (V-), U3.1 (GND), U3.4 (V-), U4.1, U4.4, U4.7 (GND), U4.10, U4.13
unnamed: J1.2, R1.2, U1.3 (-), U2.3 (-), U3.3 (-)
unnamed: J2.1, U4.3
unnamed: J2.2, U4.6
unnamed: J2.3, U4.8
unnamed: J2.4, U4.11
unnamed: J4.2, R5.1
unnamed: J5.2, U4.12
unnamed: Q1.2 (B), U1.7
unnamed: Q2.2 (B), U2.7
unnamed: Q3.2 (B), U3.7
unnamed: RV1.2, U1.2 (+)
unnamed: U1.5 (BAL), U1.6 (STRB)
unnamed: RV2.2, U2.2 (+)
unnamed: U2.5 (BAL), U2.6 (STRB)
unnamed: RV3.2, U3.2 (+)
unnamed: U3.5 (BAL), U3.6 (STRB)
TO_D0: Q3.1 (C), R4.2, U4.2
TO_D2: Q2.1 (C), R3.2, U4.5
TO_D4: Q1.1 (C), R2.2, U4.9

Notes on the sheet:
POWER
OUTPUT TO JOYSTICK
Original transistor ZTX300 is obsolete. Replaced with BC337.

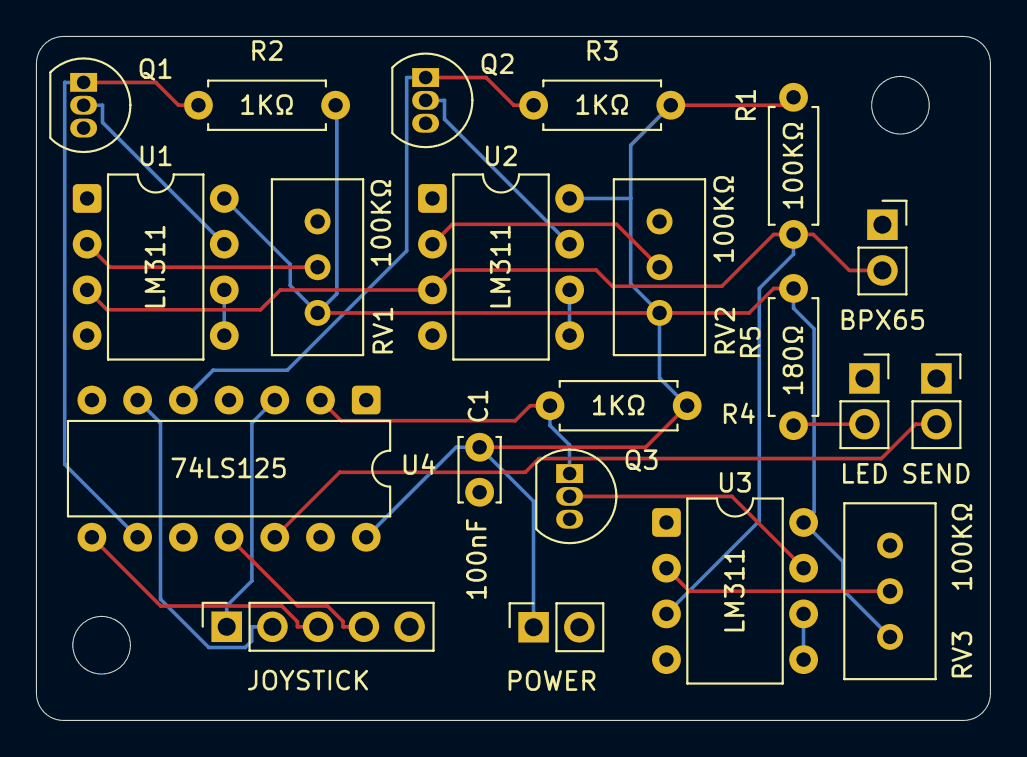
[picture p125: board Project_02_Picture_Digitiser.kicad_pcb from above]

Board: 2 copper layers, 53.0 x 38.0 mm, 23 parts (0 on the bottom side), 21 nets.
