0ddjob/Amstrad-CPC/Amstrad_CPC_Keyboard/CPC464_CPC664/Amstrad_CPC664_Keyboard.kicad_pcb

## KiCad design Amstrad_CPC_Keyboard/CPC464_CPC664/Amstrad_CPC664_Keyboard.kicad_pcb (2025-07-24)

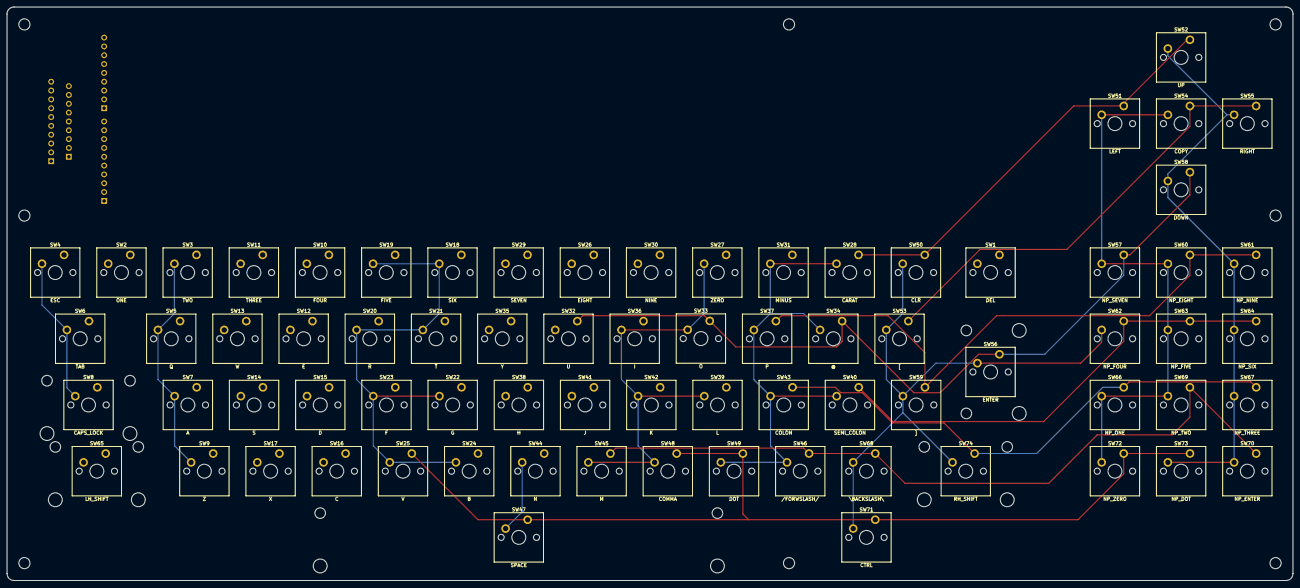
[picture p127: board Amstrad_CPC664_Keyboard.kicad_pcb from above]

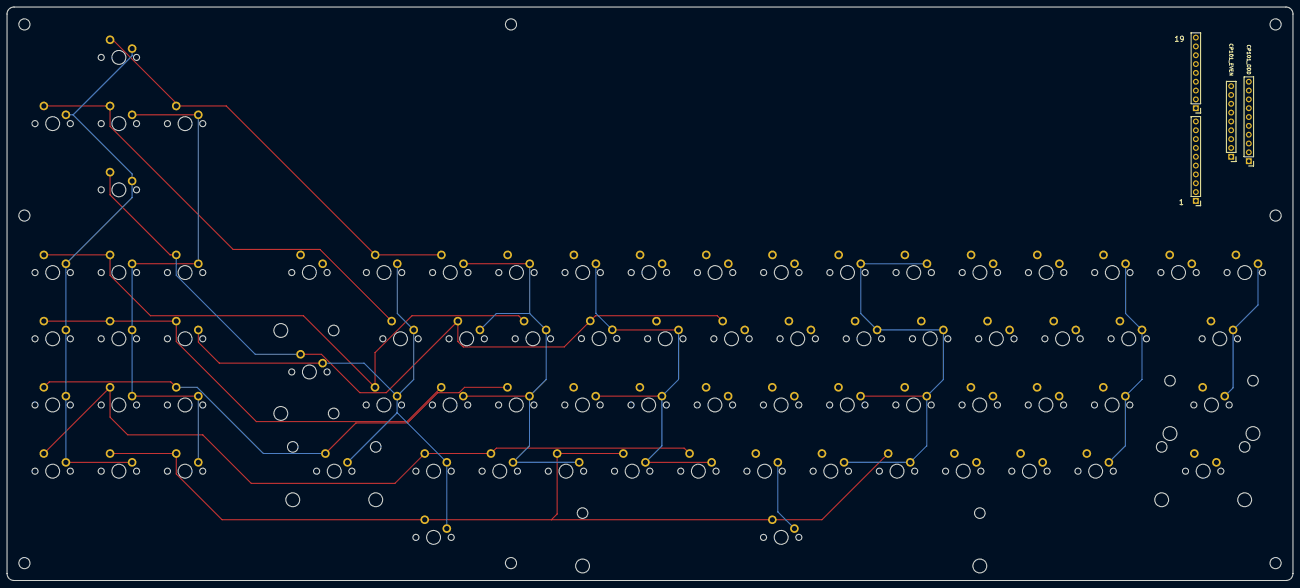
[picture p128: board Amstrad_CPC664_Keyboard.kicad_pcb from below]

Board: 2 copper layers, 370.0 x 165.0 mm, 91 parts (4 on the bottom side), 19 nets.

Parts:
H1, H2, H3, H4, H5, H6, H7, H8: MountingHole; MountingHole_3.2mm_M3
J1: CP101_ODD; PinHeader_1x10_P2.54mm_Vertical
J2: CP101_EVEN; PinHeader_1x09_P2.54mm_Vertical
J3: CP102_A; PinHeader_1x10_P2.54mm_Vertical
J4: CP102_B; PinHeader_1x09_P2.54mm_Vertical
KB8: CAPS_LOCK; Stabilizer_Cherry_MX_2.00u
KB47: SPACE; Stabilizer_Cherry_MX_7.00u
KB56: ENTER; Stabilizer_Cherry_MX_2.00u
KB65: LH_SHIFT; Stabilizer_Cherry_MX_2.00u
KB74: RH_SHIFT; Stabilizer_Cherry_MX_2.00u
SW1: DEL; SW_Cherry_MX_PCB_1.25u
SW2: ONE; SW_Cherry_MX_PCB_1.00u
SW3: TWO; SW_Cherry_MX_PCB_1.00u
SW4: ESC; SW_Cherry_MX_PCB_1.00u
SW5: Q; SW_Cherry_MX_PCB_1.00u
SW6: TAB; SW_Cherry_MX_PCB_1.75u
SW7: A; SW_Cherry_MX_PCB_1.00u
SW8: CAPS_LOCK; SW_Cherry_MX_PCB_2.00u
SW9: Z; SW_Cherry_MX_PCB_1.00u
SW10: FOUR; SW_Cherry_MX_PCB_1.00u
SW11: THREE; SW_Cherry_MX_PCB_1.00u
SW12: E; SW_Cherry_MX_PCB_1.00u
SW13: W; SW_Cherry_MX_PCB_1.00u
SW14: S; SW_Cherry_MX_PCB_1.00u
SW15: D; SW_Cherry_MX_PCB_1.00u
SW16: C; SW_Cherry_MX_PCB_1.00u
SW17: X; SW_Cherry_MX_PCB_1.00u
SW18: SIX; SW_Cherry_MX_PCB_1.00u
SW19: FIVE; SW_Cherry_MX_PCB_1.00u
SW20: R; SW_Cherry_MX_PCB_1.00u
SW21: T; SW_Cherry_MX_PCB_1.00u
SW22: G; SW_Cherry_MX_PCB_1.00u
SW23: F; SW_Cherry_MX_PCB_1.00u
SW24: B; SW_Cherry_MX_PCB_1.00u
SW25: V; SW_Cherry_MX_PCB_1.00u
SW26: EIGHT; SW_Cherry_MX_PCB_1.00u
SW27: ZERO; SW_Cherry_MX_PCB_1.00u
SW28: CARAT; SW_Cherry_MX_PCB_1.00u
SW29: SEVEN; SW_Cherry_MX_PCB_1.00u
SW30: NINE; SW_Cherry_MX_PCB_1.00u
SW31: MINUS; SW_Cherry_MX_PCB_1.00u
SW32: U; SW_Cherry_MX_PCB_1.00u
SW33: O; SW_Cherry_MX_PCB_1.00u
SW34: @; SW_Cherry_MX_PCB_1.00u
SW35: Y; SW_Cherry_MX_PCB_1.00u
SW36: I; SW_Cherry_MX_PCB_1.00u
SW37: P; SW_Cherry_MX_PCB_1.00u
SW38: H; SW_Cherry_MX_PCB_1.00u
SW39: L; SW_Cherry_MX_PCB_1.00u
SW40: SEMI_COLON; SW_Cherry_MX_PCB_1.00u
SW41: J; SW_Cherry_MX_PCB_1.00u
SW42: K; SW_Cherry_MX_PCB_1.00u
SW43: COLON; SW_Cherry_MX_PCB_1.00u
SW44: N; SW_Cherry_MX_PCB_1.00u
SW45: M; SW_Cherry_MX_PCB_1.00u
SW46: /FORWSLASH/; SW_Cherry_MX_PCB_1.00u
SW47: SPACE; SW_Cherry_MX_PCB_7.00u
SW48: COMMA; SW_Cherry_MX_PCB_1.00u
SW49: DOT; SW_Cherry_MX_PCB_1.00u
SW50: CLR; SW_Cherry_MX_PCB_1.00u
SW51: LEFT; SW_Cherry_MX_PCB_1.00u
SW52: UP; SW_Cherry_MX_PCB_1.00u
SW53: [; SW_Cherry_MX_PCB_1.00u
SW54: COPY; SW_Cherry_MX_PCB_1.00u
SW55: RIGHT; SW_Cherry_MX_PCB_1.00u
SW56: ENTER; SW_Cherry_MX_PCB_ISOEnter
SW57: NP_SEVEN; SW_Cherry_MX_PCB_1.00u
SW58: DOWN; SW_Cherry_MX_PCB_1.00u
SW59: ]; SW_Cherry_MX_PCB_1.00u
SW60: NP_EIGHT; SW_Cherry_MX_PCB_1.00u
SW61: NP_NINE; SW_Cherry_MX_PCB_1.00u
SW62: NP_FOUR; SW_Cherry_MX_PCB_1.00u
SW63: NP_FIVE; SW_Cherry_MX_PCB_1.00u
SW64: NP_SIX; SW_Cherry_MX_PCB_1.00u
SW65: LH_SHIFT; SW_Cherry_MX_PCB_2.25u
SW66: NP_ONE; SW_Cherry_MX_PCB_1.00u
SW67: NP_THREE; SW_Cherry_MX_PCB_1.00u
SW68: \BACKSLASH\; SW_Cherry_MX_PCB_1.00u
SW69: NP_TWO; SW_Cherry_MX_PCB_1.00u
SW70: NP_ENTER; SW_Cherry_MX_PCB_1.00u
SW71: CTRL; SW_Cherry_MX_PCB_1.00u
SW72: NP_ZERO; SW_Cherry_MX_PCB_1.00u
SW73: NP_DOT; SW_Cherry_MX_PCB_1.00u
SW74: RH_SHIFT; SW_Cherry_MX_PCB_2.00u

Connections:
KB_1: J1.1, J3.1, SW1.1
KB_2: J2.1, J3.2, SW1.2
KB_3: J1.2, J3.3, SW2.2, SW10.2, SW18.2, SW26.2, SW27.2, SW28.2, SW50.2, SW51.2, SW52.2
KB_4: J2.2, J3.4, SW3.2, SW11.2, SW19.2, SW29.2, SW30.2, SW31.2, SW53.2, SW54.2, SW55.2
KB_5: J1.3, J3.5, SW4.2, SW12.2, SW20.2, SW32.2, SW33.2, SW34.2, SW56.2, SW57.2, SW58.2
KB_6: J2.3, J3.6, SW5.2, SW13.2, SW21.2, SW35.2, SW36.2, SW37.2, SW59.2, SW60.2, SW61.2
KB_7: J1.4, J3.7, SW6.2, SW14.2, SW22.2, SW38.2, SW39.2, SW40.2, SW62.2, SW63.2, SW64.2
KB_8: J2.4, J3.8, SW7.2, SW15.2, SW23.2, SW41.2, SW42.2, SW43.2, SW65.2, SW66.2, SW67.2, SW74.2
KB_9: J1.5, J3.9, SW8.2, SW16.2, SW24.2, SW44.2, SW45.2, SW46.2, SW68.2, SW69.2, SW70.2
KB_10: J2.5, J3.10, SW9.2, SW17.2, SW25.2, SW47.2, SW48.2, SW49.2, SW71.2, SW72.2, SW73.2
KB_11: J1.6, SW2.1, SW3.1, SW4.1, SW5.1, SW6.1, SW7.1, SW8.1, SW9.1
KB_12: J2.6, SW10.1, SW11.1, SW12.1, SW13.1, SW14.1, SW15.1, SW16.1, SW17.1
KB_13: J1.7, SW18.1, SW19.1, SW20.1, SW21.1, SW22.1, SW23.1, SW24.1, SW25.1
KB_14: J2.7, SW26.1, SW29.1, SW32.1, SW35.1, SW38.1, SW41.1, SW44.1, SW47.1
KB_15: J1.8, SW27.1, SW30.1, SW33.1, SW36.1, SW39.1, SW42.1, SW45.1, SW48.1
KB_16: J2.8, SW28.1, SW31.1, SW34.1, SW37.1, SW40.1, SW43.1, SW46.1, SW49.1
KB_17: J1.9, SW50.1, SW53.1, SW56.1, SW59.1, SW62.1, SW65.1, SW68.1, SW71.1, SW74.1
KB_18: J2.9, SW51.1, SW54.1, SW57.1, SW60.1, SW63.1, SW66.1, SW69.1, SW72.1
KB_19: J1.10, SW52.1, SW55.1, SW58.1, SW61.1, SW64.1, SW67.1, SW70.1, SW73.1
